hevet/ESP32_radio_evo3/Hardware/Datasheets/3.12 SSD1322 OLED display/312-OLED pure glass dimensions.jpg

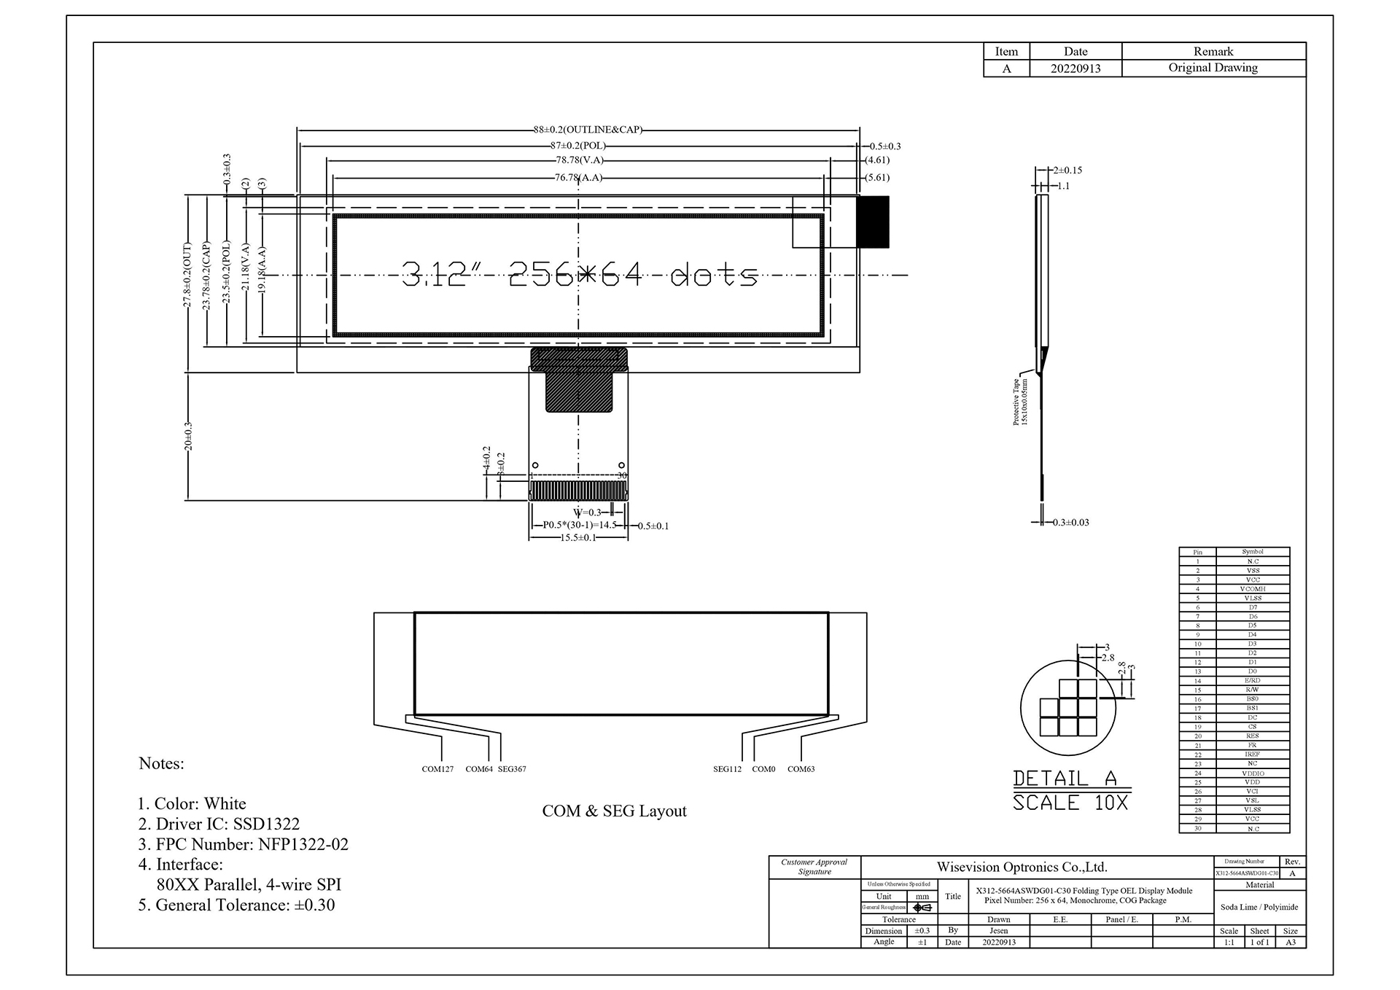
Hardware/Datasheets/3.12 SSD1322 OLED display/312-OLED pure glass dimensions.jpg
