hevet/ESP32_radio_evo3/Hardware/Datasheets/3.12 SSD1322 OLED display/OLED_pinout.png

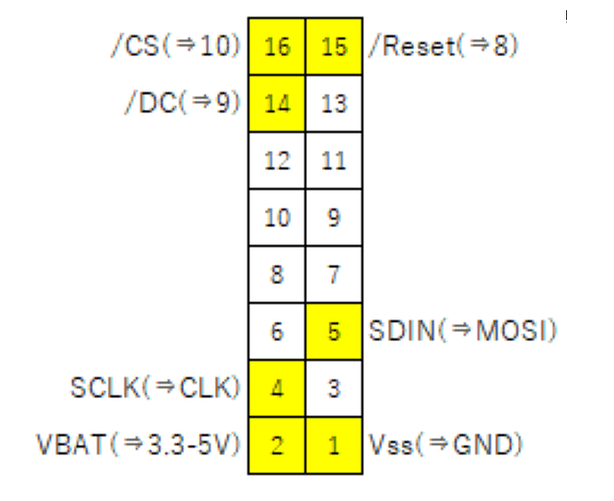
Hardware/Datasheets/3.12 SSD1322 OLED display/OLED_pinout.png
