hevet/ESP32_radio_evo3/Hardware/Datasheets/ESP/esp32 module.webp

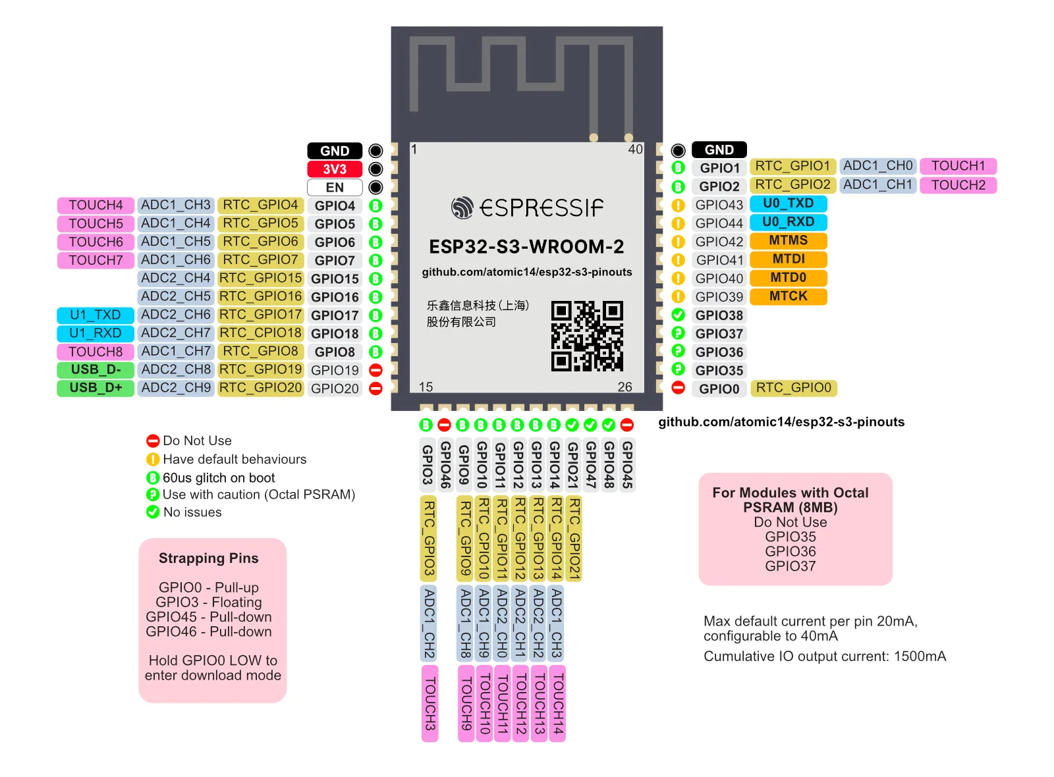
Hardware/Datasheets/ESP/esp32 module.webp
