hevet/ESP32_radio_evo3/Photos/Display1.png

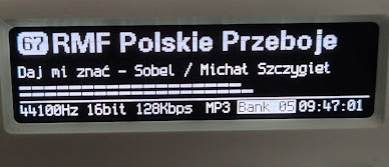
Photos/Display1.png
