hevet/ESP32_radio_evo3/Photos/Display2.png

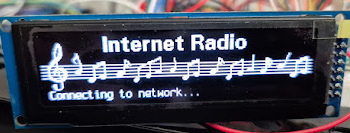
Photos/Display2.png
