hevet/ESP32_radio_evo3/Photos/ESP32_PCB_vis01.png

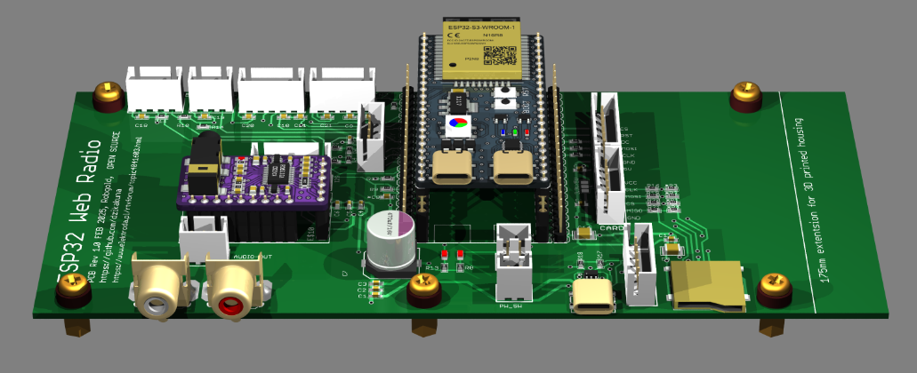
Photos/ESP32_PCB_vis01.png
