hevet/ESP32_radio_evo3/Photos/ESP_radio_rev1.0_PCBvis2.png

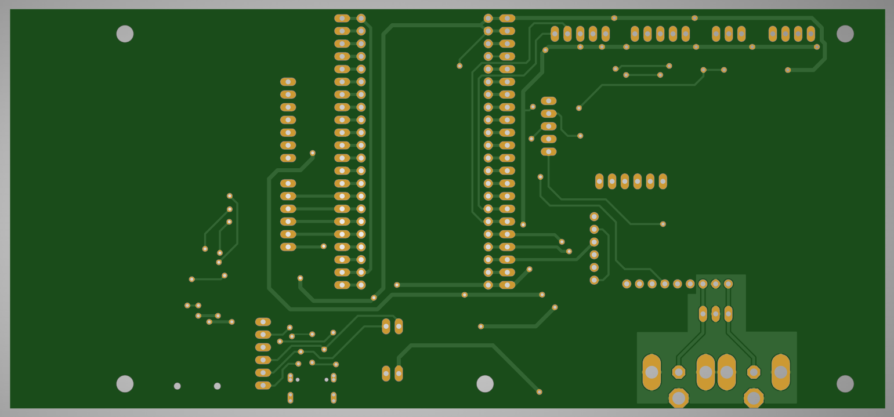
Photos/ESP_radio_rev1.0_PCBvis2.png
