hevet/ESP32_radio_evo3/Photos/Housing1.png

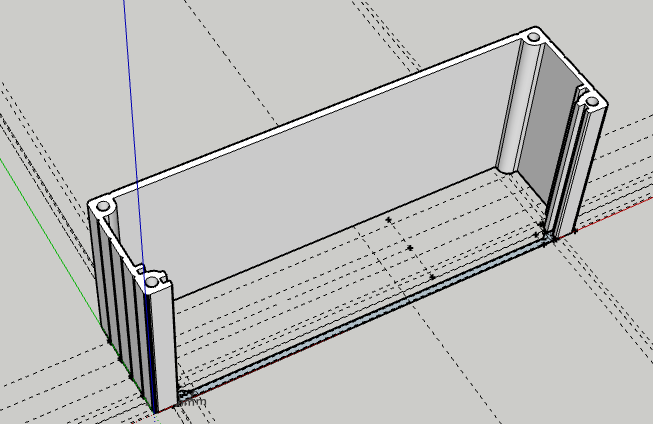
Photos/Housing1.png
