hevet/ESP32_radio_evo3/Photos/Housing3.png

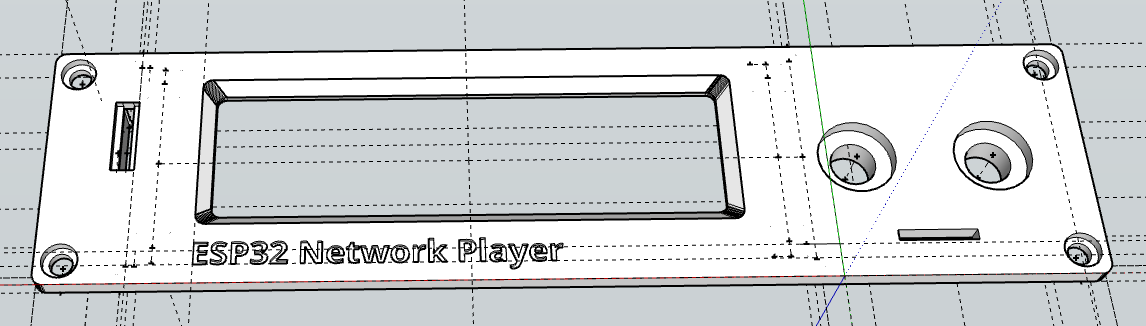
Photos/Housing3.png
