hevet/ESP32_radio_evo3/Photos/Housing4.png

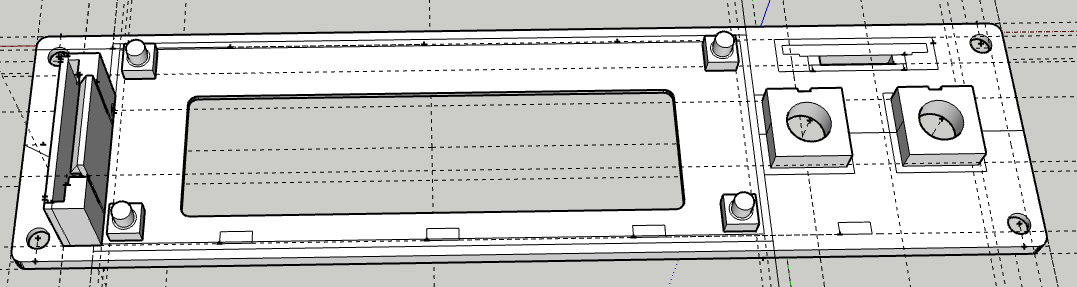
Photos/Housing4.png
