hevet/ESP32_radio_evo3/Photos/RC-406.png

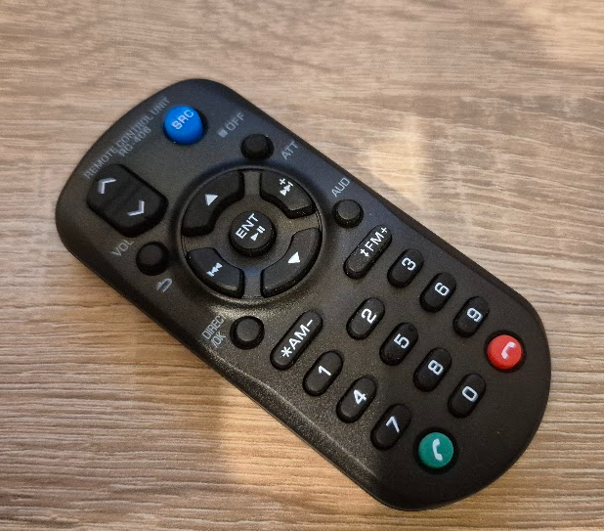
Photos/RC-406.png
