hevet/ESP32_radio_evo3/src/ESP32_radio_evo3.19/Arduino_configuration_from3.17.png

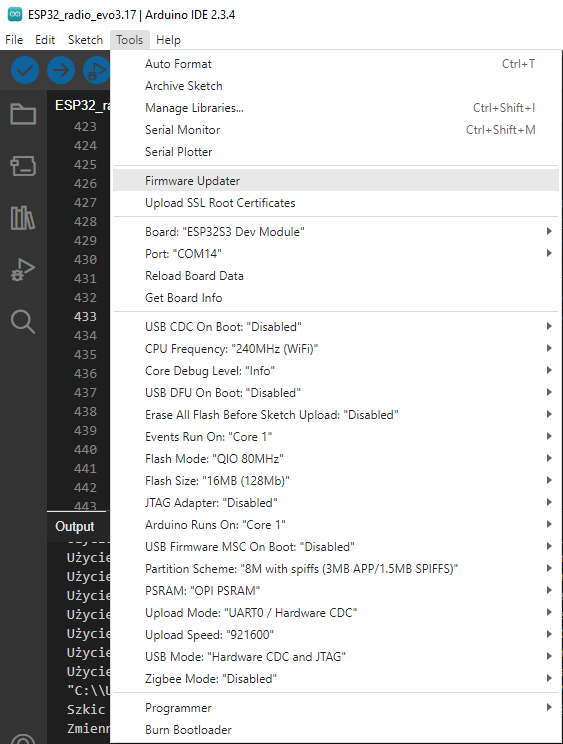
src/ESP32_radio_evo3.19/Arduino_configuration_from3.17.png
