hevet/ESP32_radio_evo3/src/ESP32_radio_evo3.19/Platformio/libdeps/ESP32-audioI2S/additional_info/Breadboard.jpg

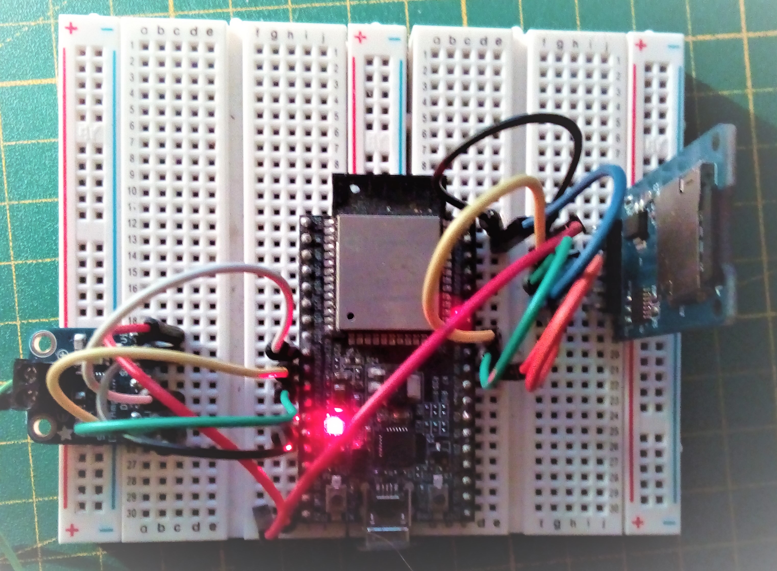
src/ESP32_radio_evo3.19/Platformio/libdeps/ESP32-audioI2S/additional_info/Breadboard.jpg
