hevet/ESP32_radio_evo3/src/ESP32_radio_evo3.19/Platformio/libdeps/ESP32-audioI2S/additional_info/ESP32_I2S_UDA1334A.JPG

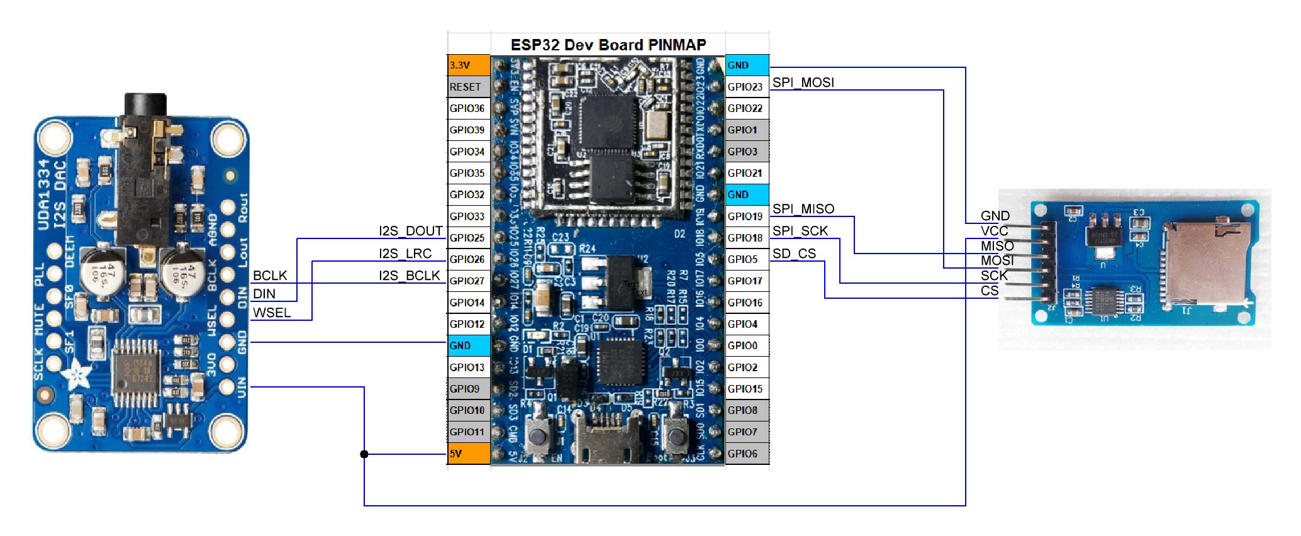
src/ESP32_radio_evo3.19/Platformio/libdeps/ESP32-audioI2S/additional_info/ESP32_I2S_UDA1334A.JPG
