hevet/ESP32_radio_evo3/src/ESP32_radio_evo3.19/Platformio/libdeps/ESP32-audioI2S/additional_info/FLAC Metadata Picture Block.jpg

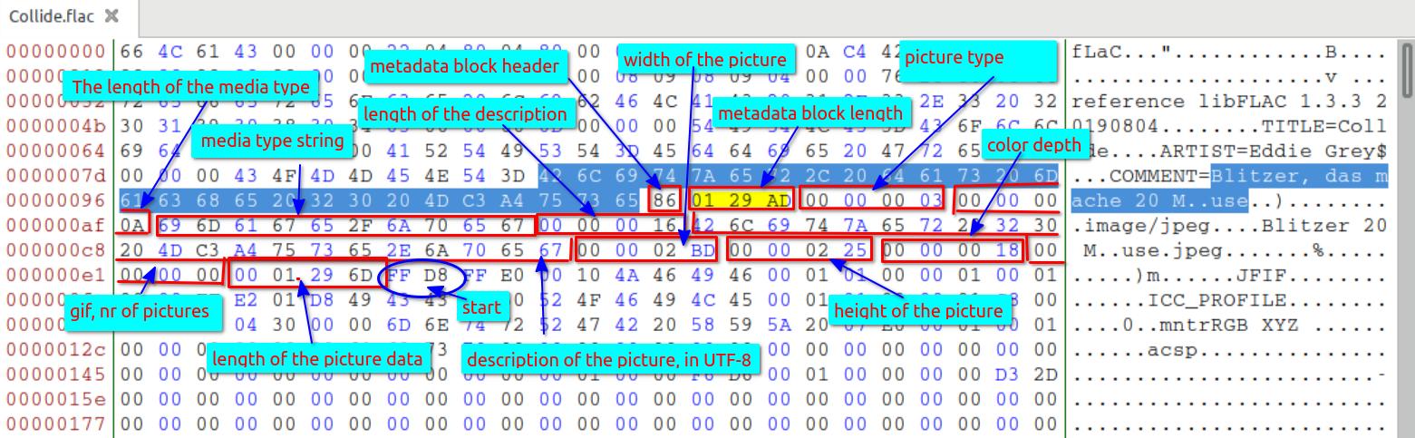
src/ESP32_radio_evo3.19/Platformio/libdeps/ESP32-audioI2S/additional_info/FLAC Metadata Picture Block.jpg
