hevet/ESP32_radio_evo3/src/ESP32_radio_evo3.19/Platformio/libdeps/ESP32-audioI2S/additional_info/Ogg_Metadatapicture.png

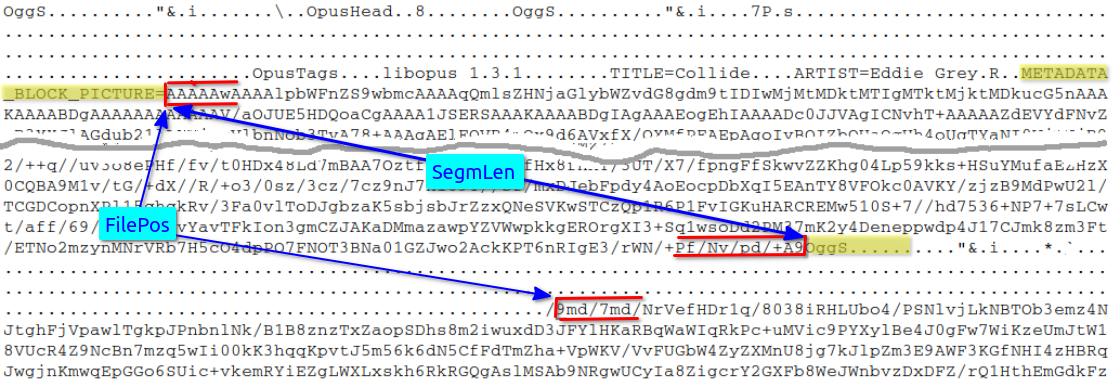
src/ESP32_radio_evo3.19/Platformio/libdeps/ESP32-audioI2S/additional_info/Ogg_Metadatapicture.png
