hevet/ESP32_radio_evo3/src/ESP32_radio_evo3.19/Platformio/libdeps/ESP32-audioI2S/examples/ESP32_A1S/AI-Thinker ESP32-Audio-Kit.jpg

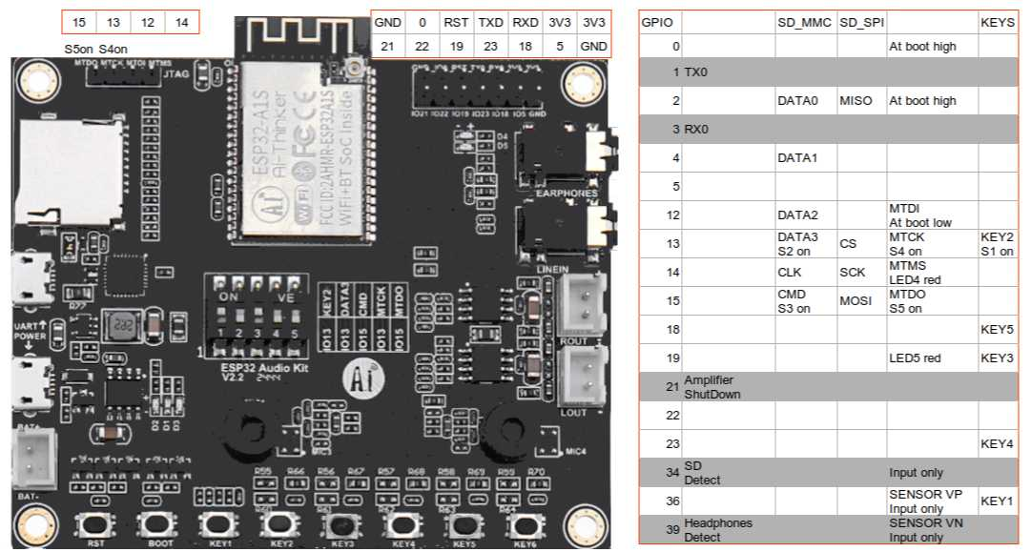
src/ESP32_radio_evo3.19/Platformio/libdeps/ESP32-audioI2S/examples/ESP32_A1S/AI-Thinker ESP32-Audio-Kit.jpg
