hevet/ESP32_radio_evo3/src/ESP32_radio_evo3.19/Platformio/libdeps/ESP32-audioI2S/examples/ESP32_TTGO-TAudio/T9V1.5.jpg

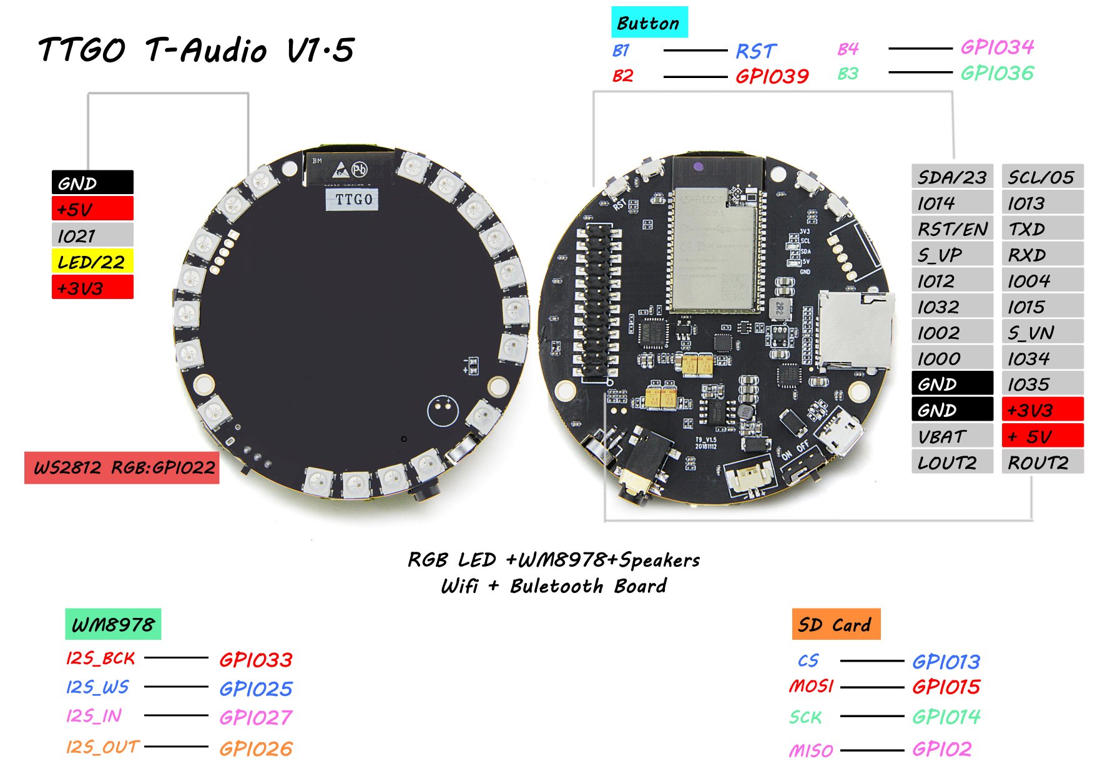
src/ESP32_radio_evo3.19/Platformio/libdeps/ESP32-audioI2S/examples/ESP32_TTGO-TAudio/T9V1.5.jpg
