hevet/ESP32_radio_evo3/src/ESP32_radio_evo3.20/Arduino/ESP32_radio_evo3.20.14.ino

// ################################################################################################################### //
// Evo Internet Radio                                                                                                  //
// ################################################################################################################### //
// Author:   Robgold 2026, Made in Poland                                                                              //
// Source -> https://github.com/dzikakuna/ESP32_radio_evo3/tree/main/src/ESP32_radio_evo3.20                           //
// ################################################################################################################### //
// Platform:                                                                                                           //
// ESP32-S3 DevModule with PSRAM -> best choice ESP32S3-16N8                                                           //
// DAC: PCM5102                                                                                                        //
// OLED Display: 2.08in, 3.12in, 5.5in 256x64px SSD1322, SH1122                                                        //
// 1x or 2x Rotary Encoder                                                                                             //
//                                                                                                                     //
//                                                                                                                     //
// Compilator: Arduino, Platformio                                                                                     //
// ESP32 by Espressif for Arduino:              3.3.8                                                                  //
// ESP32 by Espressif (for lwip recompilation): 5.5.4 - used for FLAC file station TCP/IP lwip recompilation           //
// ESP32-audioI2S-master by schreibfaul1:       3.4.5q with commits 07.05.2026                                         //
// ESP Async WebServer:                         3.10.0                                                                 //
// Async TCP:                                   3.4.10                                                                 // 
// ezButton:                                    1.0.6                                                                  //
// U8g2 by Oliver Olikraus:                     2.35.30                                                                //
// WiFiManager by tzapu                         2.0.17                                                                 //
// ################################################################################################################### //

#include "Arduino.h"           // Standardowy nagłówek Arduino, który dostarcza podstawowe funkcje i definicje
#include <WiFiManager.h>       // Biblioteka do zarządzania konfiguracją sieci WiFi, opis jak ustawić połączenie WiFi przy pierwszym uruchomieniu jest opisany tu: https://github.com/tzapu/WiFiManager
#include <Audio.h>             // Biblioteka do obsługi funkcji związanych z dźwiękiem i audio
#include "SPI.h"               // Biblioteka do obsługi komunikacji SPI
#include "FS.h"                // Biblioteka do obsługi systemu plików
#include <U8g2lib.h>           // Biblioteka do obsługi wyświetlaczy
#include <ezButton.h>          // Biblioteka do obsługi enkodera z przyciskiem
#include <HTTPClient.h>        // Biblioteka do wykonywania żądań HTTP, umożliwia komunikację z serwerami przez protokół HTTP
#include <Ticker.h>            // Mechanizm tickera do odświeżania timera 1s, pomocny do cyklicznych akcji w pętli głównej
#include <EEPROM.h>            // Bilbioteka obsługi emulacji pamięci EEPROM
#include <Time.h>              // Biblioteka do obsługi funkcji związanych z czasem, np. odczytu daty i godziny
#include <ESPAsyncWebServer.h> // Bliblioteka asyncrhionicznego serwera web
#include <AsyncTCP.h>          // Bliblioteka TCP dla serwera web
#include <Update.h>            // Blibioteka dla aktulizacji OTA
#include <ESPmDNS.h>           // Blibioteka mDNS dla ESP

#include "soc/rtc_cntl_reg.h"   // Biblioteki ESP aby móc zrobic pełny reset 
#include "soc/rtc_cntl_struct.h"// Biblioteki ESP aby móc zrobic pełny reset 
#include <esp_sleep.h>
#include "esp_system.h"

#include "esp_heap_caps.h"

#include <freertos/semphr.h>  // Semaphor uzywana w sniferze OLED
#include "esp_sntp.h"         // NTP Sync do sprawdzania stanu

#include "esp_idf_version.h"
//#include "rom/gpio.h"     // Biblioteka do mapowania pinu CS_SD
//#include "esp_wifi.h"     // Biblioteka do ustawienia pasma 20MHz


// --------------- DEFINICJA WERSJI RADIA i NAZWY HOSTA ---------------
#define softwareRev "v3.20.14"  // Wersja oprogramowania radia
#define hostname "evoradio"     // Definicja nazwy hosta widoczna w sieci
// --------------------------------------------------------------------
   
// ################ KONFIGURACJA UZYTKOWNIKA - START ################
//--------------- Typ wysweitlacza OLED ---------------
#define SSD1322     // Wyswietlacz OLED 3.12 cala, SSD1322-256x64px 
//#define SSD1309     // Wyswietlacz OLED 2.42 cala, SSD1309-128x64px TYLKO DisplayMode7 !
//#define SH1122      // Wyswietlacz OLED 2.08 cala, SSD1122-256x64px 
//#define SSD1363     // Wyswietlacz OLED 3.12 cala, SSD1322-256x128px działa ale brak trybu pełnego ekranu
//#define SSD1306     // Wyswietlacz OLED 0.96 cala, SSD1306-128x64px TYLKO DisplayMode7 !

//--------------- SPI wydajnosc pradowa ---------------
//#define LOWNOISESPI   // Ustawia wydajnosc pradowa pinow SPI (0 - najnizsza, niskie szumy; 3-najwyzsza, duze szumy), redukcja EMI

//--------------- OBSLUGA PAMIECI STORAGE ---------------
#define AUTOSTORAGE   // Definicja czy mamy właczony autostorage  (automatyczny wybor karta SD/ pamiec LittleFS lub SPIFFS w zaleznosci od ponizszej delkaracji)
#define USE_SD        // Uzywamy karty SD , zostawiamy w przypadku AUTOSTORAGE lub gdy chcemy tylko uzywać karty SD
//#define USE_SPIFFS  // Definijuemy czy w przypadku uzywania pamieci wewnetrznej bedzie to SPIFFS czy LittleFS. Odkomentowac TYLKO jedno LittleFS lub SPIFFS !
#define USE_LittleFS  // Patrz powyzej

//--------------- DRUGI ENKODER ---------------
//#define twoEncoders // Wlaczamy drugi enkoder

//--------------- DODATKi developerskie - Komunikacja RS232, Wzmacniacz TAS, sniffer OLED itp. ---------------
//#define SERIALCOM   // Komunikacja dwukierunkowa RS232
//#define TAS5805       // Kompilacja dla wersji ze Wzmacniacz TAS5805 z wbudowanym DAC, zakomentowac w przypadku tandardowe PCM5102
//#define OLED_SNIFF

//--------------- PRZYCISKI i LEDy definicja ---------------
//#define SW_POWER 8           // Dedykowany przycisk Power
#define STANDBY_LED 17         // LED do informowania o trybie Standby
#define IR_LED 17              // LED aktywności odbiornika IR
#define ADC_KEYBOARD_PIN 9     // GPIO Klawiatury ADC
//#define SD_LED 17            // LED aktywnosci karty SD, sygnalizacja syngału CS karty, klon pinu uzyteczny w przypadku uzywania czytnika SD
#define IR_LED_ON 0
#define IR_LED_OFF 1
#define STANDBY_LED_ON 0     // Stan GPIO LED STANDBY gdy radio w trybie SLEEP/OFF
#define STANDBY_LED_OFF 1    // Stan GPIO LED gdy radio ON

// --------------- AMP Control ---------------
#define AMP  // Wlaczenie GPIO do obslugi zalaczenia wzmacniacza 
#ifdef AMP
  #define AMP_CTRL 16 // Pin do kontroli wzmacniacza PWR lub Mute
  #define AMP_CTRL_LEVEL 1 // Poziom logiczny jaki mamy na wyjsciu AMP_CTRL przy wlaczonym radiu
#endif


// --------------- INNE ---------------
const bool f_logoSlowBrightness = 1; // Zalaczenie powolnego rozjasniania logo

// ################ KONFIGURACJA UZYTKOWNIKA - KONIEC ################


// --------------- OLED LIVE SNIFFER ---------------
#ifdef OLED_SNIFF
  //#define FB_SIZE (256*64/8)
  #include <freertos/semphr.h>
  #include "oledsniff.h"
  uint8_t snifferBuffer[FB_SIZE];
  uint8_t framebuffer[FB_SIZE];        // bufor
  SemaphoreHandle_t fbMutex;           // mutex do bezpiecznego dostępu
#endif

// --------------- TAS5805 ---------------
#ifdef TAS5805 //PowerAmp with I2S & DSP                 
  #include <Wire.h>           // I2C dla komunikacji z TI TAS5805
  #define I2C_CLK 9           // GPIO CLOCK I2C
  #define I2C_DATA 8          // GPIO DATA I2C
  #define TAS5805_ADDR 0x2D   // Adres I2C TAS5805, pull-up na ADR/#FAULT 10k podbicie adresu o 1
  
  // --------------- TAS5805 - definicja pinow AMPa z przetwornikiem ---------------
  #define I2S_DOUT 16        // Podłączenie do pinu DIN na DAC TAS
  #define I2S_BCLK 14        // Podłączenie po pinu BCK na DAC TAS
  #define I2S_LRC 15         // Podłączenie do pinu LCK na DAC TAS
  // --------------- IR odbiornik podczerwieni --------------- 
  #define recv_pin 7        // Odbiornik IR

#else // --------------- PCM5102A ---------------
  // --------------- PCM5102A - definicja pinow przetwornika ---------------
  #define I2S_DOUT 13             // Podłączenie do pinu DIN na DAC
  #define I2S_BCLK 12             // Podłączenie po pinu BCK na DAC
  #define I2S_LRC 14              // Podłączenie do pinu LCK na DAC 
  //#define I2S_MCLK 18           // Pełny I2S z MCLK dla SPDIF/TOSLINK
  
  // --------------- IR odbiornik podczerwieni ---------------
  #define recv_pin 15 // Odbiornik IR
#endif


// --------------- CZYTNIK KART SD (Opcjonalny) ---------------
#define SD_CS 47    // Pin CS (Chip Select) dla karty SD wybierany jako interfejs SPI
#define SD_SCLK 45  // Pin SCK (Serial Clock) dla karty SD
#define SD_MISO 21  // Pin MISO (Master In Slave Out) dla karty SD
#define SD_MOSI 48  // pin MOSI (Master Out Slave In) dla karty SD

// ------ AUTO WYKRYWANIE STORAGE - Karta SD / LittleFS -----
#ifdef AUTOSTORAGE
  
  #ifdef USE_SPIFFS 
    #include "SPIFFS.h"
  #endif

  #ifdef USE_LittleFS
    #include "LittleFS.h"
  #endif
  
  #include "SD.h"
  #define STORAGE (*_storage)
  bool initStorage();
  bool useSD = false;
  const char* storageTextName = nullptr;
  fs::FS* _storage = nullptr;
#else
  #ifdef USE_SD
    #include "SD.h"
    #define STORAGE SD
    #define STORAGE_BEGIN() SD.begin(SD_CS, customSPI)
    const bool useSD = true;
    #define storageTextName "SD      "

  #elif defined(USE_LittleFS) 
    #include "LittleFS.h"
    #define STORAGE LittleFS
    #define STORAGE_BEGIN() LittleFS.begin(true)  // Dla LittleFS, stabilniej działa i nie przerywa audio
    const bool useSD = false;
    #define storageTextName "LittleFS"
  
  #elif defined(USE_SPIFFS)
    #include "SPIFFS.h" 
    #define STORAGE LittleFS
    #define STORAGE_BEGIN() SPIFFS.begin(true)  // Stary system plikow dla kompatybilnosci
    const bool useSD = false;
    #define storageTextName "SPIFFS  "
  #endif 
#endif
 
// --------------- OLED Wyswietlacz - definicja pinow ---------------
#define SPI_MOSI_OLED 39  // Pin MOSI (Master Out Slave In) dla interfejsu SPI OLED
#define SPI_MISO_OLED 0   // Pin MISO (Master In Slave Out) brak dla wyswietlacza OLED
#define SPI_SCK_OLED 38   // Pin SCK (Serial Clock) dla interfejsu SPI OLED
#define CS_OLED 42        // Pin CS (Chip Select) dla interfejsu OLED
#define DC_OLED 40        // Pin DC (Data/Command) dla interfejsu OLED
#define RESET_OLED 41//-1 //41     // Pin Reset dla interfejsu OLED


// Rozmiar wysweitlacz OLED (potrzebny do wyświetlania grafiki)
#define SCREEN_WIDTH 256        // Szerokość ekranu w pikselach
#define SCREEN_HEIGHT 64        // Wysokość ekranu w pikselach

 

// --------------- ENCODER 2 (MAIN) ---------------
// Jesli jedyny to Volume/Stacje/Banki/PowerOff/PowerOn jesli z Enkoderem1 to Stacje/Banki
#define CLK_PIN2 10             // Podłączenie z pinu 10 do CLK na enkoderze
#define DT_PIN2 11              // Podłączenie z pinu 11 do DT na enkoderze lewym
#define SW_PIN2 1               // Podłączenie z pinu 1 do SW na enkoderze lewym (przycisk)

// --------------- ENCODER 1 (dodatkowy) ---------------
// Jesli zdefinionway to Volume/Mute/PowerOff/PowerOn
#ifdef twoEncoders
  #define CLK_PIN1 6              // Podłączenie z pinu 6 do CLK na enkoderze prawym
  #define DT_PIN1 5               // Podłączenie z pinu 5 do DT na enkoderze prawym
  #define SW_PIN1 4               // Podłączenie z pinu 4 do SW na enkoderze prawym (przycisk)
  const bool use2encoders = true;
  // Zmienne enkodera 1
  int CLK_state1 = 0;
  int prev_CLK_state1 = 0;
  int buttonLongPressTime1 = 150;
  int buttonSuperLongPressTime1 = 2000;
  bool action4Taken = false;        // Flaga Akcji 4 - enkoder 1, powerOFF
  bool action5Taken = false;        // Flaga Akcji 5 - enkoder 1, Menu Bank
#else
  const bool use2encoders = false;
#endif


// --------------- USTAWIENIE TIMERa dla trybu POWEROFF --------------- 
#define WAKEUP_INTERVAL_US (60ULL * 1000000ULL) // 1 minuta

// definicja dlugosci ilosci stacji w banku, dlugosci nazwy stacji w PSRAM/EEPROM, maksymalnej ilosci plikow audio (odtwarzacz)
#define MAX_STATIONS 99          // Maksymalna liczba stacji radiowych, które mogą być przechowywane w jednym banku
#define STATION_NAME_LENGTH 220  // Nazwa stacji wraz z bankiem i numerem stacji do wyświetlenia w pierwszej linii na ekranie
#define MAX_FILES 100            // Maksymalna liczba plików lub katalogów w tablicy directoriesz
#define bank_nr_max 16           // Numer jaki może osiągnac maksymalnie zmienna bank_nr czyli ilość banków
#define displayModeMax 6         // Ogrniczenie maksymalnej ilosci trybów wyswietlacza OLED

// DEBUG PRINTS - ON/OFF
#define f_debug_web_on 0         // Flaga właczenia wydruku debug_web
#define f_debug_on 0             // Flaga właczenia wydruku debug

//String STATIONS_URL1 = "https://raw.githubusercontent.com/dzikakuna/ESP32_radio_streams/main/bank01.txt";   // Adres URL do pliku z listą stacji radiowych
#define STATIONS_URL1  "https://raw.githubusercontent.com/dzikakuna/ESP32_radio_streams/main/bank01.txt"  // Adres URL do pliku z listą stacji radiowych
#define STATIONS_URL2  "https://raw.githubusercontent.com/dzikakuna/ESP32_radio_streams/main/bank02.txt"  // Adres URL do pliku z listą stacji radiowych
#define STATIONS_URL3  "https://raw.githubusercontent.com/dzikakuna/ESP32_radio_streams/main/bank03.txt"  // Adres URL do pliku z listą stacji radiowych
#define STATIONS_URL4  "https://raw.githubusercontent.com/dzikakuna/ESP32_radio_streams/main/bank04.txt"  // Adres URL do pliku z listą stacji radiowych
#define STATIONS_URL5  "https://raw.githubusercontent.com/dzikakuna/ESP32_radio_streams/main/bank05.txt"  // Adres URL do pliku z listą stacji radiowych
#define STATIONS_URL6  "https://raw.githubusercontent.com/dzikakuna/ESP32_radio_streams/main/bank06.txt"  // Adres URL do pliku z listą stacji radiowych
#define STATIONS_URL7  "https://raw.githubusercontent.com/dzikakuna/ESP32_radio_streams/main/bank07.txt"  // Adres URL do pliku z listą stacji radiowych
#define STATIONS_URL8  "https://raw.githubusercontent.com/dzikakuna/ESP32_radio_streams/main/bank08.txt"  // Adres URL do pliku z listą stacji radiowych
#define STATIONS_URL9  "https://raw.githubusercontent.com/dzikakuna/ESP32_radio_streams/main/bank09.txt"  // Adres URL do pliku z listą stacji radiowych
#define STATIONS_URL10 "https://raw.githubusercontent.com/dzikakuna/ESP32_radio_streams/main/bank10.txt"  // Adres URL do pliku z listą stacji radiowych
#define STATIONS_URL11 "https://raw.githubusercontent.com/dzikakuna/ESP32_radio_streams/main/bank11.txt"  // Adres URL do pliku z listą stacji radiowych
#define STATIONS_URL12 "https://raw.githubusercontent.com/dzikakuna/ESP32_radio_streams/main/bank12.txt"  // Adres URL do pliku z listą stacji radiowych
#define STATIONS_URL13 "https://raw.githubusercontent.com/dzikakuna/ESP32_radio_streams/main/bank13.txt"  // Adres URL do pliku z listą stacji radiowych
#define STATIONS_URL14 "https://raw.githubusercontent.com/dzikakuna/ESP32_radio_streams/main/bank14.txt"  // Adres URL do pliku z listą stacji radiowych
#define STATIONS_URL15 "https://raw.githubusercontent.com/dzikakuna/ESP32_radio_streams/main/bank15.txt"  // Adres URL do pliku z listą stacji radiowych
#define STATIONS_URL16 "https://raw.githubusercontent.com/dzikakuna/ESP32_radio_streams/main/bank16.txt"  // Adres URL do pliku z listą stacji radiowych
#define STATIONS_URL17 "https://raw.githubusercontent.com/dzikakuna/ESP32_radio_streams/main/bank17.txt"  // Adres URL do pliku z listą stacji radiowych
#define STATIONS_URL18 "https://raw.githubusercontent.com/dzikakuna/ESP32_radio_streams/main/bank18.txt"  // Adres URL do pliku z listą stacji radiowych


// --------------- DEFINICJA TEKSTOW ---------------
#define SLEEP_STRING "SLEEP "
#define SLEEP_STRING_VAL " MINUTES"
#define SLEEP_STRING_OFF "OFF"

#ifdef LANG_EN
static const char* months[] = {
    "JANUARY",
    "FEBRUARY",
    "MARCH",
    "APRIL",
    "MAY",
    "JUNE",
    "JULY",
    "AUGUST",
    "SEPTEMBER",
    "OCTOBER",
    "NOVEMBER",
    "DECEMBER"
};
#endif

// --------------- KOMUNIKACJA MODUŁU RADIA PO RS232 ---------------
#ifdef SERIALCOM
  #include "serialcom.h"   // Integracja jako moduł z komunikacja po RS232
#endif


// --------------- Zmienne  DLA PILOTa IR w standardzie NEC - przeniesiona do pliku txt ---------------
uint16_t rcCmdVolumeUp = 0;   // Głosnosc +
uint16_t rcCmdVolumeDown = 0; // Głośnosc -
uint16_t rcCmdArrowRight = 0; // strzałka w prawo - nastepna stacja
uint16_t rcCmdArrowLeft = 0;  // strzałka w lewo - poprzednia stacja  
uint16_t rcCmdArrowUp = 0;    // strzałka w góre - lista stacji krok do gory
uint16_t rcCmdArrowDown = 0;  // strzałka w dół - lista stacj krok na dół
uint16_t rcCmdBack = 0;	      // Przycisk powrotu
uint16_t rcCmdOk = 0;         // Przycisk Ent - zatwierdzenie stacji
uint16_t rcCmdSrc = 0;        // Przełączanie źródła radio, odtwarzacz
uint16_t rcCmdMute = 0;       // Wyciszenie dzwieku
uint16_t rcCmdAud = 0;        // Equalizer dzwieku
uint16_t rcCmdDirect = 0;     // Janość ekranu, dwa tryby 1/16 lub pełna janość     
uint16_t rcCmdBankMinus = 0;  // Wysweitla wybór banku
uint16_t rcCmdBankPlus = 0;   // Wysweitla wybór banku
uint16_t rcCmdRed = 0;        // Przełacza ładowanie banku kartaSD - serwer GitHub w menu bank
uint16_t rcCmdGreen = 0;      // VU wyłaczony, VU tryb 1, VU tryb 2, zegar
uint16_t rcCmdKey0 = 0;       // Przycisk "0"
uint16_t rcCmdKey1 = 0;       // Przycisk "1"
uint16_t rcCmdKey2 = 0;       // Przycisk "2"
uint16_t rcCmdKey3 = 0;       // Przycisk "3"
uint16_t rcCmdKey4 = 0;       // Przycisk "4"
uint16_t rcCmdKey5 = 0;       // Przycisk "5"
uint16_t rcCmdKey6 = 0;       // Przycisk "6"
uint16_t rcCmdKey7 = 0;       // Przycisk "7"
uint16_t rcCmdKey8 = 0;       // Przycisk "8"
uint16_t rcCmdKey9 = 0;       // Przycisk "9"
uint16_t rcCmdPower = 0;       // Przycisk Power
// Koniec definicji pilota IR

bool  f_callInfo = 0;       // Flaga czy wsiwetlamy "INFO" również na OLED
bool  f_logo = 0;           // Flaga czy wyswietlamy logo
bool  f_simpleMode3 =0;

int currentSelection = 0;                     // Numer aktualnego wyboru na ekranie OLED
int firstVisibleLine = 0;                     // Numer pierwszej widocznej linii na ekranie OLED
uint8_t station_nr = 0;                       // Numer aktualnie wybranej stacji radiowej z listy
int stationFromBuffer = 0;                    // Numer stacji radiowej przechowywanej w buforze do przywrocenia na ekran po bezczynności
uint8_t bank_nr;                              // Numer aktualnie wybranego banku stacji z listy
uint8_t previous_bank_nr = 0;                 // Numer banku przed wejsciem do menu zmiany banku
//int bankFromBuffer = 0;                       // Numer aktualnie wybranego banku stacji z listy do przywrócenia na ekran po bezczynności

//Enkoder 2 (podstawowy)
int CLK_state2;                               // Aktualny stan CLK enkodera lewego
int prev_CLK_state2;                          // Poprzedni stan CLK enkodera lewego
int stationsCount = 0;                        // Aktualna liczba przechowywanych stacji w tablicy
int buttonLongPressTime2 = 2000;              // Czas reakcji na długie nacisniecie enkoder 2
int buttonShortPressTime2 = 500;              // Czas rekacjinna krótkie nacisniecie enkodera 2
int buttonSuperLongPressTime2 = 3000;         // Czas reakcji na super długie nacisniecie enkoder 2

uint8_t volumeValue = 10;                     // Wartość głośności, domyślnie ustawiona na 10
uint8_t maxVolume = 21;
bool maxVolumeExt =  false;                   // 0(false) -  zakres standardowy Volume 1-21 , 1 (true) - zakres rozszerzony 0-42
uint8_t volumeBufferValue = 0;                // Wartość głośności, jako bufor w przypadku gdy nie zapisujemy za kazdym razem przy zmianie volumeValue, słuzy do porownania w momencie zapisu czy nastapila zmiana
int maxVisibleLines = 4;                      // Maksymalna liczba widocznych linii na ekranie OLED
int bitrateStringInt = 0;                     // Deklaracja zmiennej do konwersji Bitrate string na wartosc Int aby podzelic bitrate przez 1000
int SampleRate = 0;
int SampleRateRest = 0;
int audioBufferTime = 0;                      // Zienna trzymajca informacje o ilosci sekund muzyki w buforze audio

uint8_t stationNameLenghtCut = 24;            // 24-> 25 znakow, 25-> 26 znaków, zmienna określająca jak długa nazwę ma nazwa stacji w plikach Bankow liczone od 0- wartosci ustalonej
const uint8_t yPositionDisplayScrollerMode0 = 33;   // Wysokosc (y) wyswietlania przewijanego/stalego tekstu stacji w danym trybie
const uint8_t yPositionDisplayScrollerMode1 = 61;   // Wysokosc (y) wyswietlania przewijanego/stalego tekstu stacji w danym trybie
const uint8_t yPositionDisplayScrollerMode2 = 25;   // Wysokosc (y) wyswietlania przewijanego/stalego tekstu stacji w danym trybie
const uint8_t yPositionDisplayScrollerMode3 = 49;   // Wysokosc (y) wyswietlania przewijanego/stalego tekstu stacji w danym trybie
const uint8_t yPositionDisplayScrollerMode5 = 35;   // Wysokosc (y) wyswietlania przewijanego/stalego tekstu stacji w danym trybie
const uint8_t stationNamePositionYmode3 = 31;
const uint8_t stationNamePositionYmode5 = 26;
uint16_t stationStringScrollLength = 0;
uint8_t maxStationVisibleStringScrollLength = 46;
bool stationNameFromStream = 0;               // Flaga definiujaca czy wyswietlamy nazwe stacji z plikow Banku pamieci czy z informacji nadawanych w streamie
bool f_powerOff = 0;                          // Flaga aktywnego trybu power off (ESP light sleep)
bool f_sleepTimerOn = false;
uint8_t sleepTimerValueSet = 0;           // Zmiena przechowujaca ustawiony czas - nie uzywana obecnie
uint8_t sleepTimerValueCounter = 0;         // Licznik funkcji sleep timer dekrementowany przez Timer3 co 1 minute
uint8_t sleepTimerValueStep = 15;           // Krok funkcji sleep timer o ile zwieksza się timer
uint8_t sleepTimerValueMax = 90;            // Maksymalna wartosc sleep timera jaka da się ustawić
//uint8_t bank_nr_max = 16;


// ---- Głosowe odtwarzanie czasu co godzinę ---- //
bool f_requestVoiceTimePlay = false; 
bool timeVoiceInfoEveryHour = true;
unsigned long voiceTimeMillis = 0;
uint16_t voiceTimeReturnTime = 4000;


// ---- Auto dimmer / auto przyciemnianie wyswietlacza ---- //
uint8_t displayDimmerTimeCounter = 0;  // Zmienna inkrementowana w przerwaniu timera2 do przycimniania wyswietlacz
uint8_t dimmerDisplayBrightness = 10;   // Wartość przyciemnienia wyswietlacza po czasie niekatywnosci
uint8_t dimmerSleepDisplayBrightness = 1; // Wartość przyciemnienia wyswietlacza po czasie niekatywnosci
uint8_t displayBrightness = 180;        // Domyślna maksymalna janość wyswietlacza
uint16_t displayAutoDimmerTime = 5;   // Czas po jakim nastąpi przyciemninie wyswietlacza, liczony w sekundach
bool displayAutoDimmerOn = false;       // Automatyczne przyciemnianie wyswietlacza, domyślnie włączone
bool displayDimmerActive = false;       // Aktywny tryb przyciemnienia
uint16_t displayPowerSaveTime = 30;    // Czas po jakim zostanie wyłączony wyswietlacz OLED (tryb power save)
uint16_t displayPowerSaveTimeCounter = 0;    // Timer trybu Power Save wyswietlacza OLED
bool displayPowerSaveEnabled = false;   // Flaga okreslajaca czy tryb wyłączania wyswietlacza OLED jest właczony
uint8_t displayMode = 0;               // Tryb wyswietlacza 0-displayRadio z przewijaniem "scroller" / 1-Zegar / 2- tryb 3 stałych linijek tekstu stacji

// ---- Equalzier ---- //
int8_t toneLowValue = 0;               // Wartosc filtra dla tonow niskich
int8_t toneMidValue = 0;               // Wartosc flitra dla tonow srednich
int8_t toneHiValue = 0;                // Wartość filtra dla tonow wysokich
int8_t balanceValue = 0;                // Wartość balansu
uint8_t toneSelect = 1;                // Zmienna okreslająca, który filtr equalizera regulujemy, startujemy od pierwszego

bool equalizerMenuEnable = false;      // Flaga wyswietlania menu Equalizera

// ------ Wprowadzaeni cyfr z pilota / klawiatury ------ //
uint8_t rcInputDigit1 = 0xFF;      // Pierwsza cyfra w przy wprowadzaniu numeru stacji z pilota
uint8_t rcInputDigit2 = 0xFF;      // Druga cyfra w przy wprowadzaniu numeru stacji z pilota
bool f_Presets = false;            // Flaga Preset okreslajaca czy przelaczamy stacje czy wprowadzamy numer stacji jako cyfry


// ---- Zmienne konfiguracji ---- //
#define CONFIG_COUNT 27                                  // Dlugosc konfiguracji radia
uint16_t configArray[CONFIG_COUNT] = {0};
uint8_t rcPage = 0;
#define CONFIGREMOTE_COUNT 26                           // Dlugosc konfiguracji pilota IR
uint16_t configRemoteArray[CONFIGREMOTE_COUNT] = {0};   // Tablica przechowująca kody pilota podczas odczytu z pliku


uint16_t configAdcArray[24] = {0};        // Tablica przechowująca wartosci ADC dla przyciskow klawiatury
bool configExist = true;                  // Flaga okreslajaca czy istnieje plik konfiguracji
bool f_displayPowerOffClock = false;      // Flaga okreslajaca czy w trybie sleep ma się wyswietlac zegar
bool f_sleepAfterPowerFail = false;       // Flaga czy idziemy do powerOFF po powrocie zasilania
bool f_saveVolumeStationAlways = true;    // Flaga określająca czy zapisujemy stacje, bank i poziom volume zawsze czy tylko przy power OFF
bool f_powerOffAnimation = false;         // Animacja przy power OFF
bool remoteConfig = false;

bool encoderButton2 = false;      // Flaga określająca, czy przycisk enkodera 2 został wciśnięty
bool encoderFunctionOrder = false; // Flaga okreslająca kolejność funkcji enkodera 2
bool displayActive = false;       // Flaga określająca, czy wyświetlacz jest aktywny

bool mp3 = false;                 // Flaga określająca, czy aktualny plik audio jest w formacie MP3
bool flac = false;                // Flaga określająca, czy aktualny plik audio jest w formacie FLAC
bool aac = false;                 // Flaga określająca, czy aktualny plik audio jest w formacie AAC
bool vorbis = false;              // Flaga określająca, czy aktualny plik audio jest w formacie VORBIS
bool opus = false;
bool timeDisplay = true;          // Flaga określająca kiedy pokazać czas na wyświetlaczu, domyślnie od razu po starcie
bool listedStations = false;      // Flaga określająca czy na ekranie jest pokazana lista stacji do wyboru
bool bankMenuEnable = false;      // Flaga określająca czy na ekranie jest wyświetlone menu wyboru banku
bool bitratePresent = false;      // Flaga określająca, czy na serial terminalu pojawiła się informacja o bitrate - jako ostatnia dana spływajaca z info
bool bankNetworkUpdate = false;   // Flaga wyboru aktualizacji banku z sieci lub karty SD - True aktulizacja z interNETu
bool volumeMute = false;          // Flaga okreslająca stan funkcji wyciszczenia - Mute
bool volumeSet = false;           // Flaga wejscia menu regulacji głosnosci na enkoderze 2

bool action3Taken = false;        // Flaga Akcji 3

bool ActionNeedUpdateTime = false;// Zmiena okresaljaca dla displayRadio potrzebe odczytu aktulizacji czasu
bool debugAudioBuffor = false;    // Wyswietlanie bufora Audio
bool f_audioInfoRefreshStationString = false;    // Flaga wymuszjąca wymagane odsiwezenie ze względu na zmianę info stream - stationstring, title, 
bool f_audioInfoRefreshDisplayRadio = false;    // Flaga wymuszjąca wymagane odsiwezenie ze względu na zmianę info stream - linia kbps, khz, format streamu
bool resumePlay = false;            // Flaga wymaganego uruchomienia odtwarzania po zakonczeniu komunikatu głosowego
bool fwupd = false;               // Flaga blokujaca main loop podczas aktualizacji oprogramowania
bool configIrExist = false;       // Flaga informująca o istnieniu poprawnej konfiguracji pilota IR
bool wsAudioRefresh = false;      // Flaga informujaca o potrzebe odswiezeninia Station Text za pomoca Web Sokcet
bool f_voiceTimeBlocked = false;
bool f_displaySleepTime = false;    // Flaga wysiwetlania menu timera
bool f_displaySleepTimeSet = false;    // Flaga ustawienia sleep timera

bool noSDcard = false;              // flaga ustawiana przy braku wykrycia karty SD
bool noStorage = false;             // flaga ustawiana przy problemie z pamiecia SPIFFS/LittleFS

bool f_changeStationWithoutEncoderClick = false; // faga ustalajca reakcje czy automatycznie zmieniamy stacje po wybraniu na liscie stacji

unsigned long debounceDelay = 300;    // Czas trwania debouncingu w milisekundach
unsigned long displayTimeout = 3000;  // Czas wyświetlania komunikatu na ekranie w milisekundach
unsigned long displayStartTime = 0;   // Czas rozpoczęcia wyświetlania komunikatu
unsigned long seconds = 0;            // Licznik sekund timera
unsigned int PSRAM_lenght = MAX_STATIONS * (STATION_NAME_LENGTH) + MAX_STATIONS; // deklaracjia długości pamięci PSRAM
unsigned long lastCheckTime = 0;      // No stream audio blink
//uint8_t stationNameStreamWidth = 0;   // Test pełnej nazwy stacji
uint64_t seconds2nextMinute;
uint64_t micros2nextMinute;

// ---- VU Meter ---- //
unsigned long vuMeterTime;                 // Czas opznienia odswiezania wskaznikow VU w milisekundach
uint8_t vuMeterL;                          // Wartosc VU dla L kanału zakres 0-255
uint8_t vuMeterR;                          // Wartosc VU dla R kanału zakres 0-255
uint8_t peakL = 0;                         // Wartosc peakHold dla kanalu lewego
uint8_t peakR = 0;                         // Wartosc peakHold dla kanalu prawego
uint8_t peakHoldTimeL = 0;                 // Licznik peakHold dla kanalu lewego
uint8_t peakHoldTimeR = 0;                 // Licznik peakHold dla kanalu prawego
const uint8_t peakHoldThreshold = 5;       // Liczba cykli zanim peak opadnie
const uint8_t vuLy = 41;                   // Koordynata Y wskaznika VU L-lewego (wyzej)
const uint8_t vuRy = 47;                   // Koordynata Y wskaznika VU R-prawego (nizej)
const uint8_t vuLyMode3 = 54;              // Koordynata Y wskaznika VU L-lewego (wyzej)
const uint8_t vuRyMode3 = 60;              // Koordynata Y wskaznika VU R-prawego (nizej
const uint8_t vuLyMode5 = 43;                   // Koordynata Y wskaznika VU L-lewego (wyzej)
const uint8_t vuRyMode5 = 49;                   // Koordynata Y wskaznika VU R-prawego (nizej)
const uint8_t vuThicknessMode3 = 1;        // Grubosc kreseczki wskaznika VU w trybie Mode3
const int vuCenterXmode3 = 128;            // Pozycja centralna startu VU w trybie Mode 3
const int vuYmode3 = 62;                   // Polozenie wyokosci (Y) VU w trybie Mode 3
bool vuPeakHoldOn = 1;                     // Flaga okreslajaca czy funkcja Peak & Hold na wskazniku VUmeter jest wlaczona
bool vuMeterOn = true;                     // Flaga właczajaca wskazniki VU
bool vuMeterMode = false;                  // tryb rysowania vuMeter
uint8_t displayVuL = 0;                    // wartosc VU do wyswietlenia po procesie smooth
uint8_t displayVuR = 0;                    // wartosc VU do wyswietlenia po procesie smooth
uint8_t vuRiseSpeed = 24;                  // szybkość narastania VU
uint8_t vuFallSpeed = 6;                   // szybkość opadania VU
bool vuSmooth = 1;                         // Flaga zalaczenia funkcji smootht (domyslnie wlaczona=1)
uint8_t vuRiseNeedleSpeed = 2;                  // szybkość narastania VU
uint8_t vuFallNeedleSpeed = 6;                   // szybkość opadania VU
bool reversColorMode4 = true;

// Volume Fade
unsigned long lastFadeTime = 0;
const unsigned long fadeStepDelay = 20; // ms
bool fadingIn = false;
uint8_t targetVolume = 0;
uint8_t currentVolume = 0;
bool f_volumeFadeOn = 0;
uint8_t volumeFadeOutTime = 20; //ms * volumeValue
uint8_t volumeSleepFadeOutTime = 50;

unsigned long scrollingStationStringTime;  // Czas do odswiezania scorllingu
uint8_t scrollingRefresh = 50;              // Czas w ms przewijania tekstu funkcji Scroller

uint8_t vuMeterRefreshCounterSet = 0;      // Mnoznik co ile petli loopRefreshTime ma byc odswiezony VU Meter
uint8_t scrollerRefreshCounterSet = 0;     // Mnoznik co ile petli loopRefreshTime ma byc odswiezony i przewiniety o 1px Scroller

uint16_t stationStringScrollWidth;         // szerokosc Stringu nazwy stacji w funkcji Scrollera
uint16_t xPositionStationString = 0;       // Pozycja początkowa dla przewijania tekstu StationString
uint16_t offset;                           // Zminnna offsetu dla funkcji Scrollera - przewijania streamtitle na ekranie OLED
unsigned char * psramData;                 // zmienna do trzymania danych stacji w pamieci PSRAM

unsigned long vuMeterMilisTimeUpdate;           // Zmienna przechowujaca czas dla funkci millis VU Meter refresh
uint8_t vuMeterRefreshTime = 50;                // Czas w ms odswiezania VUmetera

uint8_t wifiSignalLevel = 0;
uint8_t wifiSignalLevelLast = 7;          // Pamiecm poprzedniego stanu signalLevel

// ---- Serwer Web ---- //
unsigned long currentTime = millis();
unsigned long previousTime = 0;
const long timeoutTime = 2000;
bool urlToPlay = false;   // Flaga czy mamy uruchomic stream przekazany przez strone www
bool urlPlaying = false; // Flaga czy gramy z adresu URL ze strony www


// ---- Sprawdzenie funkcji pilota, zminnne do pomiaru róznicy czasów ---- //
unsigned long runTime = 0;
unsigned long runTime1 = 0;
unsigned long runTime2 = 0;


String stationStringScroll = "";     // Zmienna przechowująca tekst do przewijania na ekranie
String stationName;                  // Nazwa aktualnie wybranej stacji radiowej
String stationString;                // Dodatkowe dane stacji radiowej (jeśli istnieją)
String stationStringWeb;                // Dodatkowe dane stacji radiowej (jeśli istnieją)
String bitrateString;                // Zmienna przechowująca informację o bitrate
String sampleRateString;             // Zmienna przechowująca informację o sample rate
String bitsPerSampleString;          // Zmienna przechowująca informację o liczbie bitów na próbkę
String currentIP;
String stationNameStream;           // Nazwa stacji wyciągnieta z danych wysylanych przez stream
String streamCodec;
String stationLogoUrl;
String timezone;


String header;                      // Zmienna dla serwera www
String sliderValue = "0";
String url2play = "";


File myFile;  // Uchwyt pliku

//U8G2_SSD1322_NHD_256X64_F_4W_HW_SPI u8g2(U8G2_R2, /* cs=*/CS_OLED, /* dc=*/DC_OLED, /* reset=*/RESET_OLED);  // Hardware SPI 3.12inch OLED
//U8G2_SSD1309_128X64_NONAME0_F_4W_HW_SPI u8g2(U8G2_R2, /* cs=*/CS_OLED, /* dc=*/DC_OLED, /* reset=*/RESET_OLED);  
//U8G2_SH1122_256X64_F_4W_HW_SPI u8g2(U8G2_R2, /* cs=*/ CS_OLED, /* dc=*/ DC_OLED, /* reset=*/ RESET_OLED);		// Hardware SPI  2.08inch OLED
//U8G2_SSD1363_256X128_F_4W_HW_SPI u8g2(U8G2_R0, /* cs=*/CS_OLED, /* dc=*/DC_OLED, /* reset=*/RESET_OLED);  // Hardware SPI 3.12inch OLED

#if defined(SSD1322)
  U8G2_SSD1322_NHD_256X64_F_4W_HW_SPI u8g2(U8G2_R2, CS_OLED, DC_OLED, RESET_OLED);
#elif defined(SSD1309)
  U8G2_SSD1309_128X64_NONAME0_F_4W_HW_SPI u8g2(U8G2_R2, CS_OLED, DC_OLED, RESET_OLED);
#elif defined(SH1122)
  U8G2_SH1122_256X64_F_4W_HW_SPI u8g2(U8G2_R2, CS_OLED, DC_OLED, RESET_OLED);
#elif defined(SSD1363) 
  U8G2_SSD1363_256X128_F_4W_HW_SPI u8g2(U8G2_R0, CS_OLED, DC_OLED, RESET_OLED);
#elif defined(SSD1306)   
  U8G2_SSD1306_128X64_NONAME_F_4W_HW_SPI u8g2(U8G2_R0, CS_OLED, DC_OLED, RESET_OLED);
#else
  #error "Nie wybrano typu wyswietlacza!"
#endif


// Przypisujemy port serwera www
AsyncWebServer server(80);
AsyncWebSocket ws("/ws"); //Start obsługi Websocketów


// Inicjalizacja WiFiManagera
WiFiManager wifiManager;


// Konfiguracja nowego SPI z wybranymi pinami dla czytnika kart SD
SPIClass customSPI = SPIClass(HSPI);  // Używamy HSPI, ale z własnymi pinami

#ifdef twoEncoders
  ezButton button1(SW_PIN1);  // Utworzenie obiektu przycisku z enkodera 2 ezButton
#endif

ezButton button2(SW_PIN2);  // Utworzenie obiektu przycisku z enkodera 2 ezButton
Audio audio;                // Obiekt do obsługi funkcji związanych z dźwiękiem i audio

Ticker timer1;             // Timer do aktualizacji Zegara
Ticker timer2;             // Timer funkcji Dimmer
Ticker timer3;             // Timer dla funkcji Sleep
Ticker timer4;             // Timer startu migania LED
//Ticker timer5;             // Timer probkowania klawiatury ADC
WiFiClient client;         // Obiekt do obsługi połączenia WiFi dla klienta HTTP


// ------------------- STRON HTML zaszyte w kodzie -------------------
const char stylehead_html[] PROGMEM = R"rawliteral(
  <!DOCTYPE HTML><html>
  <head>
    <link rel='icon' href='/favicon.ico' type='image/x-icon'>
    <link rel="shortcut icon" href="/favicon.ico" type="image/x-icon">
    <link rel="apple-touch-icon" sizes="180x180" href="/icon.png">
    <link rel="icon" type="image/png" sizes="192x192" href="/icon.png">

    <meta name="viewport" content="width=device-width, initial-scale=1">
    <title>Evo Web Radio</title>
    <style>
      html {font-family: Arial; display: inline-block; text-align: center;}
      h2 {font-size: 1.3rem;}
      p {font-size: 0.95rem;}
      table {border: 1px solid black; border-collapse: collapse; margin: 0px 0px;}
      td, th {font-size: 0.8rem; border: 1px solid gray; border-collapse: collapse;}
      td:hover {font-weight:bold;}
      a {color: black; text-decoration: none;}
      body {max-width: 1380px; margin:0px auto; padding-bottom: 25px; background: #D0D0D0;}
      .slider {-webkit-appearance: none; margin: 14px; width: 330px; height: 10px; background: #4CAF50; outline: none; -webkit-transition: .2s; transition: opacity .2s; border-radius: 5px;}
      .slider::-webkit-slider-thumb {-webkit-appearance: none; appearance: none; width: 35px; height: 25px; background: #4a4a4a; cursor: pointer; border-radius: 5px;}
      .slider::-moz-range-thumb { width: 35px; height: 35px; background: #4a4a4a; cursor: pointer; border-radius: 5px;} 
      .button { background-color: #4CAF50; border: 1; color: white; padding: 10px 20px; border-radius: 5px;}
      .buttonBank { background-color: #4CAF50; border: 1; color: white; padding: 8px 8px; border-radius: 5px; width: 35px; height: 35px; margin: 0 1.5px;}
      .buttonBankSelected { background-color: #505050; border: 1; color: white; padding: 8px 8px; border-radius: 5px; width: 35px; height: 35px; margin: 0 1.5px;}
      .buttonBank:active {background-color: #4a4a4a; box-shadow: 0 4px #666; transform: translateY(2px);}
      .buttonBank:hover {background-color: #4a4a4a;}
      .button:hover {background-color: #4a4a4a;}
      .button:active {background-color: #4a4a4a; box-shadow: 0 4px #666; transform: translateY(2px);}
      .column {padding: 5px; display: flex; justify-content: space-between;}
      .columnlist {padding: 10px; display: flex; justify-content: center;}
      .stationList {text-align:left; margin-top: 0px; width: 280px; margin-bottom:0px;cursor: pointer;}
      .stationNumberList {text-align:center; margin-top: 0px; width: 35px; margin-bottom:0px;}
      .stationListSelected {text-align:left; margin-top: 0px; width: 280px; margin-bottom:0px;cursor: pointer; background-color: #4CAF50;}
      .stationNumberListSelected {text-align:center; margin-top: 0px; width: 35px; margin-bottom:0px; background-color: #4CAF50;}
      .station-name {}  
    </style>
  </head>
)rawliteral";

const char index_html[] PROGMEM = R"rawliteral(
  <!DOCTYPE HTML><html>
  <head>
    <link rel='icon' href='/favicon.ico' type='image/x-icon'>
    <link rel="shortcut icon" href="/favicon.ico" type="image/x-icon">
    <link rel="apple-touch-icon" sizes="180x180" href="/icon.png">
    <link rel="icon" type="image/png" sizes="192x192" href="/icon.png">

    <meta name="viewport" content="width=device-width, initial-scale=1">
    <title>Evo Web Radio</title>
    <style>
      html {font-family: Arial; display: inline-block; text-align: center;}
      h2 {font-size: 1.3rem;}
      p {font-size: 0.95rem;}
      table {border: 1px solid black; border-collapse: collapse; margin: 0px 0px;}
      td, th {font-size: 0.8rem; border: 1px solid gray; border-collapse: collapse;}
      td:hover {font-weight:bold;}
      a {color: black; text-decoration: none;}
      body {max-width: 1380px; margin:0px auto; padding-bottom: 25px; background: #D0D0D0;}
      .slider {-webkit-appearance: none; margin: 14px; width: 330px; height: 10px; background: #4CAF50; outline: none; -webkit-transition: .2s; transition: opacity .2s; border-radius: 5px;}
      .slider::-webkit-slider-thumb {-webkit-appearance: none; appearance: none; width: 35px; height: 25px; background: #4a4a4a; cursor: pointer; border-radius: 5px;}
      .slider::-moz-range-thumb { width: 35px; height: 35px; background: #4a4a4a; cursor: pointer; border-radius: 5px;} 
      .button { background-color: #4CAF50; border: 1; color: white; padding: 10px 20px; border-radius: 5px;}
      .buttonBank { background-color: #4CAF50; border: 1; color: white; padding: 8px 8px; border-radius: 5px; width: 35px; height: 35px; margin: 0 1.5px;}
      .buttonBankSelected { background-color: #505050; border: 1; color: white; padding: 8px 8px; border-radius: 5px; width: 35px; height: 35px; margin: 0 1.5px;}
      .buttonBank:active {background-color: #4a4a4a box-shadow: 0 4px #666; transform: translateY(2px);}
      .buttonBank:hover {background-color: #4a4a4a;}
      .button:hover {background-color: #4a4a4a;}
      .button:active {background-color: #4a4a4a; box-shadow: 0 4px #666; transform: translateY(2px);}
      .column { align: center; padding: 5px; display: flex; justify-content: space-between;}
      .columnlist { align: center; padding: 10px; display: flex; justify-content: center;}
      .stationList {text-align:left; margin-top: 2px; width: 280px; height:18px; margin-bottom:0px;cursor: pointer;}
      .stationNumberList {text-align:center; margin-top: 2px; width: 35px; height:18px; margin-bottom:0px;}
      .stationListSelected {text-align:left; margin-top: 2px; width: 280px; height:18px; margin-bottom:0px;cursor: pointer; background-color: #4CAF50;}
      .stationNumberListSelected {text-align:center; margin-top: 2px; width: 35px; height:18px; margin-bottom:0px; background-color: #4CAF50;} 
      .wifi-wrapper {display: flex; align-items: flex-end; gap: 1px; height: 13px; margin-top: -3px; margin-bottom: 3px; justify-content: center; }
      .wifiBar {width: 2px;background-color: #555; border-radius: 2px; transition: background-color 0.2s;}
      .bar1 { height: 2px; }
      .bar2 { height: 4px; }
      .bar3 { height: 6px; }
      .bar4 { height: 8px; }
      .bar5 { height: 10px; }
      .bar6 { height: 12px; }
    </style>
  </head>

  <body>
    <h2>Evo Web Radio</h2>
  
    <div id="display" style="display: inline-block; padding: 6px; border: 2px solid #4CAF50; border-radius: 15px; background-color: #4a4a4a; font-size: 1.45rem; 
      color: #AAA; width: 345px; text-align: center; white-space: nowrap; box-shadow: 0 0 20px #4CAF50;" onClick="flashBackground(); displayMode()">
      
      <div style="margin-bottom: 10px; font-weight: bold; overflow: hidden; text-overflow: ellipsis; -webkit-text-stroke: 0.3px black; text-stroke: 0.3px black;">
        <span id="textStationName"><b>STATIONNAME</b></span>
      </div>
      
      <div style="width: 345px; margin-bottom: 10px;">
        <div id="stationTextDiv" style="display: block; text-overflow: ellipsis; white-space: normal; font-size: 1.0rem; color: #999; margin-bottom: 10px; text-align: center; align-items: center; height: 4.2em; justify-content: center; overflow: hidden; line-height: 1.4em;">
          <span id="stationText">STATIONTEXT</span>
        </div>
        <div id="muteIndicatorDiv" style="text-align:center; color:#4CAF50; font-weight:bold; font-size:1.0rem; height:1.4em; margin-top:-5px;">
        <span id="muteIndicator"></span>
        </div>
      </div>
      
      <div style="height: 1px; background-color: #4CAF50; margin: 5px 0;"></div>

      
      <div style="display: flex; justify-content: center; gap: 13px; font-size: 1.00rem; color: #999;">
        <div><span id="bankValue">Bank: --</span></div>
          <div style="display: flex; justify-content: center; gap: 6px; font-size: 0.55rem; color: #999;margin: 4px 0;">
            <div><span id="samplerate">---.-kHz</span></div>
            <div><span id="bitrate">---kbps</span></div>
            <div><span id="bitpersample">---bit</span></div>
            <div><span id="streamformat">----</span></div>
            WiFi: <div class="wifi-wrapper">
            <div class="wifiBar bar1" id="wifiBar1"></div>
            <div class="wifiBar bar2" id="wifiBar2"></div>
            <div class="wifiBar bar3" id="wifiBar3"></div>
            <div class="wifiBar bar4" id="wifiBar4"></div>
            <div class="wifiBar bar5" id="wifiBar5"></div>
            <div class="wifiBar bar6" id="wifiBar6"></div>
  	      </div>
        </div>
        <div><span id="stationNumber">Station: --</span></div>
      </div>

  </div>
  <br>
  <br>
  <script>

  var websocket;

  function updateSliderVolume(element) 
  {
    var sliderValue = document.getElementById("volumeSlider").value;
    document.getElementById("textSliderValue").innerText = sliderValue;

    if (websocket && websocket.readyState === WebSocket.OPEN) 
    {
      websocket.send("volume:" + sliderValue);
    } 
    else 
    {
      console.warn("WebSocket niepołączony");
    }
  }

  function changeStation(number) 
  {
    if (websocket.readyState === WebSocket.OPEN) 
    {
      websocket.send("station:" + number);
    } 
    else 
    {
      console.log("WebSocket nie jest otwarty");
    }
  }

  function changeBank(number) 
  {
    if (websocket.readyState === WebSocket.OPEN) 
    {
      websocket.send("bank:" + number);
    } 
    else 
    {
      console.log("WebSocket nie jest otwarty");
    }
  }


  function displayMode() 
  {
    //fetch("/displayMode")
    if (websocket.readyState === WebSocket.OPEN) 
    {
      websocket.send("displayMode");
    } 
    else 
    {
      console.log("WebSocket nie jest otwarty");
    }
  }
  
  function setWifi(level) 
  {
    for (let i = 1; i <= 6; i++) 
    {
      const bar = document.getElementById("wifiBar" + i);
      if (bar) {bar.style.backgroundColor = (i <= level) ? "#4CAF50" : "#555";}
    }
  }


  function connectWebSocket() 
  {
    websocket = new WebSocket('ws://' + window.location.hostname + '/ws');
    websocket.onopen = function () 
    {
      console.log("WebSocket polaczony");
    };
    
    websocket.onclose = function (event) 
    {
      console.log("WebSocket zamkniety. Proba ponownego polaczenia za 3 sekundy...");
      setTimeout(connectWebSocket, 3000); // próba ponownego połączenia
    };

    websocket.onerror = function (error) 
    {
      console.error("Blad WebSocket: ", error);
      websocket.close(); // zamyka połączenie, by wywołać reconnect
    };
    
    websocket.onmessage = function(event) 
    {
      if (event.data === "reload") 
      {
        location.reload();
      }  
      
      if (event.data.startsWith("volume:")) 
      {
        var vol = parseInt(event.data.split(":")[1]);
        document.getElementById("volumeSlider").value = vol;
        document.getElementById("textSliderValue").innerText = vol;
      }
      
      if (event.data.startsWith("station:")) 
      {
        var station = parseInt(event.data.split(":")[1]);
        highlightStation(station);
        //document.getElementById('stationNumber').innerText = event.data.split(':')[1];
        document.getElementById('stationNumber').innerText ='Station: ' + station; 
      }
      
      if (event.data.startsWith("stationname:")) 
      {
        var value = event.data.split(":")[1];
        document.getElementById("textStationName").innerHTML = `<b>${value}</b>`;
        //checkStationTextLength();
      }  

      if (event.data.startsWith("stationtext$")) 
      {
        //var stationtext = event.data.split("$")[1];
        //document.getElementById("stationText").innerHTML = `${stationtext}`;
        
        var stationtext = event.data.substring(event.data.indexOf("$") + 1);
        //document.getElementById("stationText").innerHTML = stationtext;       
        document.getElementById("stationText").textContent = stationtext;
      }  

      if (event.data.startsWith("bank:")) 
      {
        var bankValue = parseInt(event.data.split(":")[1]);
        document.getElementById('bankValue').innerText = 'Bank: ' + bankValue;
      } 

      //if (event.data.startsWith("samplerate:")) 
      //{
      //  var samplerate = parseInt(event.data.split(":")[1]);
      //  var formattedRate = (samplerate / 1000).toFixed(1) + "kHz";
      //  document.getElementById('samplerate').innerText = formattedRate;
      //}
      
      if (event.data.startsWith("samplerate:")) 
      {
        var raw = event.data.split(":")[1];
        var samplerate = parseInt(raw);

        if (isNaN(samplerate)) 
        {
          document.getElementById('samplerate').innerText = '---.-kHz';
        } 
        else 
        {
          var formattedRate = (samplerate / 1000).toFixed(1) + "kHz";
          document.getElementById('samplerate').innerText = formattedRate;
        }
      }

      //if (event.data.startsWith("bitrate:")) 
      //{	
      //  var bitrate = parseInt(event.data.split(":")[1]);
      //  document.getElementById('bitrate').innerText = bitrate + 'kbps';
      //}

      if (event.data.startsWith("bitrate:")) 
      {	
        var raw = event.data.split(":")[1];
        var bitrate = parseInt(raw);

        if (isNaN(bitrate)) 
        {
          document.getElementById('bitrate').innerText = '---kbps';
        } 
        else 
        {
          document.getElementById('bitrate').innerText = bitrate + 'kbps';
        }
      }

      
      //if (event.data.startsWith("bitpersample:")) 
      //{	
      //  var bitpersample = parseInt(event.data.split(":")[1]);
      //  document.getElementById('bitpersample').innerText = bitpersample + 'bit';
      //}

      if (event.data.startsWith("bitpersample:")) 
      {	
        var raw = event.data.split(":")[1];
        var bitpersample = parseInt(raw);

        if (isNaN(bitpersample)) 
        {
          document.getElementById('bitpersample').innerText = '---bit';
        } 
        else 
        {
          document.getElementById('bitpersample').innerText = bitpersample + 'bit';
        }
      }

      
      if (event.data.startsWith("streamformat:")) 
      {	
        var streamformat = event.data.split(":")[1];
        document.getElementById('streamformat').innerText = streamformat;
      }  

      if (event.data.startsWith("mute:")) 
      {
        //var muteInd = parseInt(event.data.split(":")[1]);
        const muteInd = event.data.split(":")[1] === "1" ? 1 : 0;
        document.getElementById('muteIndicator').textContent = (muteInd === 1) ? 'MUTED' : '';       
      }

      if (event.data.startsWith("wifi:")) 
      {
        const level = parseInt(event.data.split(":")[1]);
        if (!isNaN(level)) {setWifi(Math.min(Math.max(level, 1), 6));}
      }


    }

  };
  
  function highlightStation(stationId) 
  {
    // Usuń poprzednie zaznaczenia
    document.querySelectorAll(".stationList").forEach(el => {
    el.classList.remove("stationListSelected");
    //el.innerHTML = el.dataset.stationName || el.innerText; // przywróć oryginalny numer
    el.innerText = el.dataset.stationName || el.innerText;


    });

    document.querySelectorAll(".stationNumberList").forEach(el => {
      el.classList.remove("stationNumberListSelected");
      el.innerHTML = el.dataset.stationNumber || el.innerText; // przywróć oryginalny numer
    });

    // Zaznacz nową stację
    const numCells = document.querySelectorAll(".stationNumberList");
    const stationCells = document.querySelectorAll(".stationList");

    const numCell = numCells[stationId - 1];
    const stationCell = stationCells[stationId - 1];

    if (numCell && stationCell) 
    {
      numCell.classList.add("stationNumberListSelected");
      stationCell.classList.add("stationListSelected");
      
      // Pogrub nazwę stacji
      stationCell.dataset.stationName = stationCell.innerText; // zapisz oryginalny tekst
      stationCell.innerHTML = `<b>${stationCell.innerText}</b>`; // pogrubienie nazwy stacji

      //const original = stationCell.dataset.originalName || stationCell.innerText;
      //stationCell.dataset.originalName = original;
      //stationCell.innerText = original;
      //stationCell.style.fontWeight = "bold";

        
      // Pogrub numer
      numCell.dataset.stationNumber = numCell.innerText; // zapisz oryginalny numer
      numCell.innerHTML = `<b>${numCell.innerText}</b>`; 
      //const originalNum = numCell.dataset.originalNumber || numCell.innerText;
      //numCell.dataset.originalNumber = originalNum;
      //numCell.innerText = originalNum;
      //numCell.style.fontWeight = "bold";


    }
  }
  
  function flashBackground() 
	{
	  const div = document.getElementById('display');
	  const originalColor = div.style.backgroundColor;

	  const textSpan = document.getElementById('textStationName');
    const originalText = textSpan.innerText;


	  div.style.backgroundColor = '#115522'; // kolor flash
	  //textSpan.innerText = 'OLED Display Mode Changed';
    textSpan.innerHTML = '<b>Display Mode Changed</b>';  

	  setTimeout(() => 
	  {
		  div.style.backgroundColor = originalColor;
		  //textSpan.innerText = originalText;
      textSpan.innerHTML = `<b>${originalText}</b>`;
	  }, 150); // czas w ms flasha
	}


  document.addEventListener("DOMContentLoaded", function () 
  {
    connectWebSocket(); // podlaczamy websockety

    const slider = document.getElementById("volumeSlider");
    slider.addEventListener("wheel", function (event) 
    {
      event.preventDefault(); // zapobiega przewijaniu strony

      let currentValue = parseInt(slider.value);
      const step = parseInt(slider.step) || 1;
      const max = parseInt(slider.max);
      const min = parseInt(slider.min);

      if (event.deltaY < 0) {
        // przewijanie w górę (zwiększ)
        slider.value = Math.min(currentValue + step, max);
      } else {
        // przewijanie w dół (zmniejsz)
        slider.value = Math.max(currentValue - step, min);
      }

      updateSliderVolume(slider); // wywołaj aktualizację
    });
  });

  window.onpageshow = function(event) 
  {
    if (event.persisted) 
    {
      window.location.reload();
    }
  };

 </script>
)rawliteral";

const char list_html[] PROGMEM = R"rawliteral(
  <!DOCTYPE HTML><html>
  <head>
    <link rel='icon' href='/favicon.ico' type='image/x-icon'>
    <link rel="shortcut icon" href="/favicon.ico" type="image/x-icon">
    <link rel="apple-touch-icon" sizes="180x180" href="/icon.png">
    <link rel="icon" type="image/png" sizes="192x192" href="/icon.png">

    <meta name="viewport" content="width=device-width, initial-scale=1">
    <title>Evo Web Radio</title>
    <style>
      html {font-family: Arial; display: inline-block; text-align: center;}
      h2 {font-size: 1.3rem;}
      p {font-size: 1.1rem;}
      table {border: 1px solid black; border-collapse: collapse; margin: 0px 0px;}
      td, th {font-size: 0.8rem; border: 1px solid gray; border-collapse: collapse;}
      td:hover {font-weight:bold;}
      a {color: black; text-decoration: none;}
      body {max-width: 1380px; margin:0px auto; padding-bottom: 25px;}
      .columnlist { align: center; padding: 10px; display: flex; justify-content: center;}
    </style>
  </head>
)rawliteral";

const char config_html[] PROGMEM = R"rawliteral(
  <!DOCTYPE HTML>
  <html>
  <head>
    <link rel='icon' href='/favicon.ico' type='image/x-icon'>
    <link rel="shortcut icon" href="/favicon.ico" type="image/x-icon">
    <link rel="apple-touch-icon" sizes="180x180" href="/icon.png">
    <link rel="icon" type="image/png" sizes="192x192" href="/icon.png">

    <meta name="viewport" content="width=device-width, initial-scale=1">
    <title>Evo Web Radio</title>
    <style>
      html {font-family: Arial; display: inline-block; text-align: center;}
      h1 {font-size: 2.3rem;}
      h2 {font-size: 1.3rem;}
      table {border: 1px solid black; border-collapse: collapse; margin: 20px auto; width: 80%;}
      th, td {font-size: 1rem; border: 1px solid gray; padding: 8px; text-align: left;}
      td:hover {font-weight: bold;}
      a {color: black; text-decoration: none;}
      body {max-width: 1380px; margin:0 auto; padding-bottom: 25px;}
      .tableSettings {border: 2px solid #4CAF50; border-collapse: collapse; margin: 10px auto; width: 60%;}
      input[type="checkbox"] {accent-color: #66BB6A; color: #FFFF50; width: 13px; height: 13px; }
      input[type="text"] { width: 60px; box-sizing: border-box;}
      @media (max-width:768px){.about-box,.tableSettings{width:90%!important;} table{width:100%!important;} th,td{font-size:0.9rem;}}
    </style>
    </head>

  <body>
  <h2>Evo Web Radio - Settings</h2>
  <form action="/configupdate" method="POST">
  <table class="tableSettings">
  <tr><th>Display Setting</th><th>Value</th></tr>
  <tr><td>Normal Display Brightness (0-255), default:180</td><td><input type="number" name="displayBrightness" min="1" max="255" value="%D1"></td></tr>
  <tr><td>Dimmed Display Brightness (0-200), default:20</td><td><input type="number" name="dimmerDisplayBrightness" min="1" max="200" value="%D2"></td></tr>
  <tr><td>Dimmed Display Brightness in Sleep Mode (0-50), default:1</td><td><input type="number" name="dimmerSleepDisplayBrightness" min="1" max="50" value="%D12"></td></tr>
  <tr><td>Auto Dimmer Delay Time (1-255 sec.), default:5</td><td><input type="number" name="displayAutoDimmerTime" min="1" max="255" value="%D3"></td></tr>
  <tr><td>Auto Dimmer, default:On</td><td><input type="checkbox" name="displayAutoDimmerOn" value="1" %S1_checked></td></tr>
  <tr><td>OLED Display Clock in Sleep Mode default:Off</td><td><input type="checkbox" name="f_displayPowerOffClock" value="1" %S19_checked></td></tr>
  <tr><td>OLED Display Power Save Mode, default:Off</td><td><input type="checkbox" name="displayPowerSaveEnabled" value="1" %S9_checked></td></tr>
  <tr><td>OLED Display Power Save Time (1-600sek.), default:20</td><td><input type="number" name="displayPowerSaveTime" min="1" max="600" value="%D9"></td></tr>
  <tr><td>OLED Display Mode - 0-Radio basic, 1-Clock, 2-Three lines, 3-Centered, 4-VU analog, 5-VU digital</td><td><input type="number" name="displayMode" min="0" max="5" value="%D6"></td></tr>

  <tr><th>Other Setting</th><th></th></tr>
  <tr><td>Time Voice Info Every Hour, default:On</td><td><input type="checkbox" name="timeVoiceInfoEveryHour" value="1" %S3_checked></td></tr>
  <tr><td>Encoder Function Order (0-1), 0-Volume, click for station list, 1-Station list, click for Volume</td><td><input type="number" name="encoderFunctionOrder" min="0" max="1" value="%D5"></td></tr>
  <tr><td>Radio Scroller & VU Meter Refresh Time (15-100ms), default:50</td><td><input type="number" name="scrollingRefresh" min="15" max="100" value="%D8"></td></tr>
  <tr><td>ADC Keyboard Enabled, default:Off</td><td><input type="checkbox" name="adcKeyboardEnabled" value="1" %S7_checked></td></tr>
  <tr><td>Volume Steps 1-21 [Off], 1-42 [On], default:Off</td><td><input type="checkbox" name="maxVolumeExt" value="1" %S11_checked></td></tr>
  <tr><td>Station Name Read From Stream [On-From Stream, Off-From Bank] EXPERIMENTAL</td><td><input type="checkbox" name="stationNameFromStream" value="1" %S17_checked></td></tr>
  <tr><td>Radio switch to Standby After Power Fail, default:On</td><td><input type="checkbox" name="f_sleepAfterPowerFail" value="1" %S21_checked></td></tr>
  <tr><td>Volume Fade on Station Change and Power Off, default:Off</td><td><input type="checkbox" name="f_volumeFadeOn" value="1" %S22_checked></td></tr>
  <tr><td>Save ALWAYS Station No., Bank No., Volume, default:Off</td><td><input type="checkbox" name="f_saveVolumeStationAlways" value="1" %S23_checked></td></tr>
  <tr><td>Power Off Animation, default:Off</td><td><input type="checkbox" name="f_powerOffAnimation" value="1" %S24_checked></td></tr>
  <tr><td>Timezone Settings</td><td><button type="button" class="button" onclick="location.href='/timezone'">Set</button></td></tr>
  <tr><td>Remote Control Settings</td><td><button type="button" class="button" onclick="location.href='/remoteconfig'">Set</button></td></tr>
  <tr><td>Presets On (Key 0-9 switching stations 1 to 10), default:Off</td><td><input type="checkbox" name="f_Presets" value="1" %S25_checked></td></tr>
  <tr><td>Change station from list without click, default:Off</td><td><input type="checkbox" name="f_changeStationWithoutEncoderClick" value="1" %S26_checked></td></tr>


  <tr><th><b>VU Meter Settings</b></th></tr>
  <tr><td>VU Meter Mode (0-1), 0-dashed lines, 1-continuous lines</td><td><input type="number" name="vuMeterMode" min="0" max="1" value="%D4"></td></tr>
  <tr><td>VU Meter Visible (Mode 0, 3 only), default:On</td><td><input type="checkbox" name="vuMeterOn" value="1" %S5_checked></td></tr>
  <tr><td>VU Meter Peak & Hold Function, default:On</td><td><input type="checkbox" name="vuPeakHoldOn" value="1" %S13_checked></td></tr>
  <tr><td>VU Meter Smooth Function, default:On</td><td><input type="checkbox" name="vuSmooth" value="1" %S15_checked></td></tr>
  <tr><td>VU Meter Smooth Rise Speed [1 low - 32 High], default:24</td><td><input type="number" name="vuRiseSpeed" min="1" max="32" value="%D10"></td></tr>
  <tr><td>VU Meter Smooth Fall Speed [1 low - 32 High], default:6</td><td><input type="number" name="vuFallSpeed" min="1" max="32" value="%D11"></td></tr>
  </table>
  <input type="submit" value="Update">
  </form>


  <p style='font-size: 0.8rem;'><a href='/menu'>Go Back</a></p>
  </body>
  </html>
)rawliteral";

const char remoteconfig_html[] PROGMEM = R"rawliteral(
  <!DOCTYPE HTML>
  <html>
  <head>
  <meta charset="UTF-8">
  <meta name="viewport" content="width=device-width, initial-scale=1">
  <title>Evo Web Radio</title>

  <link rel="icon" href="/favicon.ico" type="image/x-icon">
  <link rel="shortcut icon" href="/favicon.ico" type="image/x-icon">
  <link rel="apple-touch-icon" sizes="180x180" href="/icon.png">
  <link rel="icon" type="image/png" sizes="192x192" href="/icon.png">

  <style>
  html{font-family:Arial;display:inline-block;text-align:center;}
  body{max-width:1380px;margin:0 auto;padding-bottom:25px;}
  h1{font-size:2.3rem;}h2{font-size:1.3rem;}
  table{border:1px solid #000;border-collapse:collapse;margin:20px auto;width:40%;}
  th,td{font-size:1rem;border:1px solid gray;padding:8px;text-align:left;}
  td:hover{font-weight:bold;}
  tr.selected{background:#d0f0d0;}
  a{color:black;text-decoration:none;}
  .tableSettings{border:2px solid #4CAF50;border-collapse:collapse;margin:5px auto;width:40%;}
  input[type="checkbox"]{accent-color:#66BB6A;color:#FFFF50;width:13px;height:13px;}
  input[type="text"]{width:70px;box-sizing:border-box;}
  #wsBox{border:2px solid #4CAF50;padding:10px;margin:15px auto;width:38%;background:#f5fff5;font-size:1.1rem;}
  #wsDetails{padding:5px;margin:5px auto;width:100%;background:#f5fff5;font-size:0.8rem;}
  p{font-size:0.7rem;}
  #AddrValue { margin-right: 10px; font-size:0.8rem;}
  #CmdValue { margin-right: 10px; font-size:0.8rem;}
  #Learn{background:#f5fff5;font-size:0.8rem; color:#4CAF50; font-weight:bold;}
  @media(max-width:768px){.about-box,.tableSettings,#wsBox{width:90%!important;}table{width:100%!important;}th,td{font-size:.9rem;}}
  </style>
  </head>

  <body>

  <h2>Evo Web Radio - Remote Control Config</h2>

  <div id="wsBox">
    <strong>Received code:</strong> <span id="codeValue">—</span>
    <div id="wsDetails">
      <p>Address:<span id="AddrValue">—</span>  Command:<span id="CmdValue">—</span></p>
    </div>
    <div id="Learn"><span id="LearnIndicator"></span></div>
  </div>

  <p></p>

  <div style="margin:10px;">
    <button onclick="toggleRemoteConfig()">Learning Mode - ON/OFF</button>
    <label><input type="checkbox" id="autoMode">AUTO Mode</label>&nbsp;&nbsp;
    <button type="button" onclick="skipCurrent()">Skip Sellected</button>
  </div>

  <p> Single Mouse Click on Row - Select, Double Mouse Click - Reset Value (set 0xFEFE)</p>
  <p> Auto Mode, auto increment and select next cell affer receiving IR code</p>

  <form action="/remoteconfigupdate" method="POST">
  <table class="tableSettings">
  <tr><th>Codes:</th><th>Value</th></tr>

  <tr><td>Volume Up +</td><td><input type="text" name="cmdVolumeUp" value="%D0" pattern="0x[0-9A-Fa-f]{4}" maxlength="6" title="Format: 0xFFFF"></td></tr>
  <tr><td>Volume Down -</td><td><input type="text" name="cmdVolumeDown" value="%D1" pattern="0x[0-9A-Fa-f]{4}" maxlength="6" title="Format: 0xFFFF"></td></tr>
  <tr><td>Arrow Right (Next Station / Next Bank)</td><td><input type="text" name="cmdArrowRight" value="%D2" pattern="0x[0-9A-Fa-f]{4}" maxlength="6" title="Format: 0xFFFF"></td></tr>
  <tr><td>Arrow Left (Prev Station / Prev Bank)</td><td><input type="text" name="cmdArrowLeft" value="%D3" pattern="0x[0-9A-Fa-f]{4}" maxlength="6" title="Format: 0xFFFF"></td></tr>
  <tr><td>Arrow Up (Station List Up)</td><td><input type="text" name="cmdArrowUp" value="%D4" pattern="0x[0-9A-Fa-f]{4}" maxlength="6" title="Format: 0xFFFF"></td></tr>
  <tr><td>Arrow Down (Station List Down)</td><td><input type="text" name="cmdArrowDown" value="%D5" pattern="0x[0-9A-Fa-f]{4}" maxlength="6" title="Format: 0xFFFF"></td></tr>

  <tr><td>Back</td><td><input type="text" name="cmdBack" value="%D6" pattern="0x[0-9A-Fa-f]{4}" maxlength="6" title="Format: 0xFFFF"></td></tr>
  <tr><td>OK / Enter</td><td><input type="text" name="cmdOk" value="%D7" pattern="0x[0-9A-Fa-f]{4}" maxlength="6" title="Format: 0xFFFF"></td></tr>

  <tr><td>Display Screen Mode</td><td><input type="text" name="cmdSrc" value="%D8" pattern="0x[0-9A-Fa-f]{4}" maxlength="6" title="Format: 0xFFFF"></td></tr>
  <tr><td>Mute</td><td><input type="text" name="cmdMute" value="%D9" pattern="0x[0-9A-Fa-f]{4}" maxlength="6" title="Format: 0xFFFF"></td></tr>
  <tr><td>Equalizer</td><td><input type="text" name="cmdAud" value="%D10" pattern="0x[0-9A-Fa-f]{4}" maxlength="6" title="Format: 0xFFFF"></td></tr>

  <tr><td>Display Brightness / Bank Network Update</td><td><input type="text" name="cmdDirect" value="%D11" pattern="0x[0-9A-Fa-f]{4}" maxlength="6" title="Format: 0xFFFF"></td></tr>

  <tr><td>Bank Menu (-)</td><td><input type="text" name="cmdBankMinus" value="%D12" pattern="0x[0-9A-Fa-f]{4}" maxlength="6" title="Format: 0xFFFF"></td></tr>
  <tr><td>Bank Menu (+)</td><td><input type="text" name="cmdBankPlus" value="%D13" pattern="0x[0-9A-Fa-f]{4}" maxlength="6" title="Format: 0xFFFF"></td></tr>

  <tr><td>Power On / Off</td><td><input type="text" name="cmdRed" value="%D14" pattern="0x[0-9A-Fa-f]{4}" maxlength="6" title="Format: 0xFFFF"></td></tr>
  <tr><td>Sleep</td><td><input type="text" name="cmdGreen" value="%D15" pattern="0x[0-9A-Fa-f]{4}" maxlength="6" title="Format: 0xFFFF"></td></tr>

  <tr><td>Key 0</td><td><input type="text" name="cmdKey0" value="%D16" pattern="0x[0-9A-Fa-f]{4}" maxlength="6" title="Format: 0xFFFF"></td></tr>
  <tr><td>Key 1</td><td><input type="text" name="cmdKey1" value="%D17" pattern="0x[0-9A-Fa-f]{4}" maxlength="6" title="Format: 0xFFFF"></td></tr>
  <tr><td>Key 2</td><td><input type="text" name="cmdKey2" value="%D18" pattern="0x[0-9A-Fa-f]{4}" maxlength="6" title="Format: 0xFFFF"></td></tr>
  <tr><td>Key 3</td><td><input type="text" name="cmdKey3" value="%D19" pattern="0x[0-9A-Fa-f]{4}" maxlength="6" title="Format: 0xFFFF"></td></tr>
  <tr><td>Key 4</td><td><input type="text" name="cmdKey4" value="%D20" pattern="0x[0-9A-Fa-f]{4}" maxlength="6" title="Format: 0xFFFF"></td></tr>
  <tr><td>Key 5</td><td><input type="text" name="cmdKey5" value="%D21" pattern="0x[0-9A-Fa-f]{4}" maxlength="6" title="Format: 0xFFFF"></td></tr>
  <tr><td>Key 6</td><td><input type="text" name="cmdKey6" value="%D22" pattern="0x[0-9A-Fa-f]{4}" maxlength="6" title="Format: 0xFFFF"></td></tr>
  <tr><td>Key 7</td><td><input type="text" name="cmdKey7" value="%D23" pattern="0x[0-9A-Fa-f]{4}" maxlength="6" title="Format: 0xFFFF"></td></tr>
  <tr><td>Key 8</td><td><input type="text" name="cmdKey8" value="%D24" pattern="0x[0-9A-Fa-f]{4}" maxlength="6" title="Format: 0xFFFF"></td></tr>
  <tr><td>Key 9</td><td><input type="text" name="cmdKey9" value="%D25" pattern="0x[0-9A-Fa-f]{4}" maxlength="6" title="Format: 0xFFFF"></td></tr>

  </table>

  <input type="submit" value="Update">
  </form>

  <p style="font-size:.8rem;"><a href="/menu">Go Back</a></p>

  <script>
  let websocket;
  let activeInput = null;
  let inputs = [];
  let currentIndex = -1;
  let autoMode = false;

  function toggleRemoteConfig() {
    const xhr = new XMLHttpRequest();
    xhr.open("POST", "/toggleRemoteConfig", true);
    xhr.send();
  }

  function clearSelection() {
    document.querySelectorAll(".tableSettings tr")
      .forEach(r => r.classList.remove("selected"));
    activeInput = null;
    currentIndex = -1;
  }

  function selectInputByIndex(index) {
    if (index >= inputs.length) {
      autoMode = false;
      document.getElementById("autoMode").checked = false;
      clearSelection();
      return;
    }

    clearSelection();
    currentIndex = index;
    activeInput = inputs[index];
    const row = activeInput.closest("tr");
    row.classList.add("selected");
    activeInput.focus();
  }

  function moveNext() {
    selectInputByIndex(currentIndex + 1);
  }

  function skipCurrent() {
    if (!activeInput) return;
    activeInput.value = "0xFEFE";
    if (autoMode) moveNext();
  }

  document.getElementById("autoMode").addEventListener("change", function () {
    autoMode = this.checked;
    if (autoMode) selectInputByIndex(0);
    else clearSelection();
  });

  document.addEventListener("DOMContentLoaded", function () {
    inputs = Array.from(
      document.querySelectorAll('.tableSettings input[type="text"]')
    );

    inputs.forEach((input, index) => {
      const row = input.closest("tr");

      row.onclick = () => selectInputByIndex(index);
      row.ondblclick = () => {
        input.value = "0xFEFE";
        selectInputByIndex(index);
      };
    });

    websocket = new WebSocket('ws://' + window.location.hostname + '/ws');

    websocket.onmessage = function (event) {
      if (event.data.startsWith("addr:"))
        document.getElementById('AddrValue').innerText = event.data.split(":")[1];

      if (event.data.startsWith("cmd:"))
        document.getElementById('CmdValue').innerText = event.data.split(":")[1];

      if (event.data.startsWith("learn:"))
        document.getElementById("LearnIndicator").innerText =
          parseInt(event.data.split(":")[1]) ? "LEARNING MODE ON" : "";

      if (event.data.startsWith("ircode:")) {
        const codeStr = event.data.split(":")[1].trim();
        document.getElementById('codeValue').innerText = codeStr;

        if (activeInput) {
          activeInput.value = codeStr;
          if (autoMode) moveNext();
        }
      }
    };
  });
  </script>

  </body>
  </html>
)rawliteral";

const char adc_html[] PROGMEM = R"rawliteral(
  <!DOCTYPE HTML>
  <html>
  <head>
    <link rel='icon' href='/favicon.ico' type='image/x-icon'>
    <link rel="shortcut icon" href="/favicon.ico" type="image/x-icon">
    <link rel="apple-touch-icon" sizes="180x180" href="/icon.png">
    <link rel="icon" type="image/png" sizes="192x192" href="/icon.png">

    <meta name="viewport" content="width=device-width, initial-scale=1">
    <title>Evo Web Radio</title>
    <style>
      html {font-family: Arial; display: inline-block; text-align: center;}
      h1 {font-size: 2.3rem;}
      h2 {font-size: 1.3rem;}
      table {border: 1px solid black; border-collapse: collapse; margin: 10px auto; width: 40%;}
      th, td {font-size: 1rem; border: 1px solid gray; padding: 8px; text-align: left;}
      td:hover {font-weight: bold;}
      a {color: black; text-decoration: none;}
      body {max-width: 1380px; margin:0 auto; padding-bottom: 15px;}
      .tableSettings {border: 2px solid #4CAF50; border-collapse: collapse; margin: 10px auto; width: 40%;}
      .button { background-color: #4CAF50; border: 1; color: white; padding: 10px 20px; border-radius: 5px; width:200px;}
      .button:hover {background-color: #4a4a4a;}
      .button:active {background-color: #4a4a4a; box-shadow: 0 4px #666; transform: translateY(2px);}
    </style>
    </head>

  <body>
  <h2>Evo Web Radio - ADC Settings</h2>
  <form action="/configadc" method="POST">
  <table class="tableSettings">
  <tr><th>Button</th><th>Value</th></tr>
  <tr><td>Key 0</td><td><input type="number" name="keyboardButtonThreshold_0" min="0" max="4100" value="%D0"></td></tr>
  <tr><td>Key 1</td><td><input type="number" name="keyboardButtonThreshold_1" min="0" max="4100" value="%D1"></td></tr>
  <tr><td>Key 2</td><td><input type="number" name="keyboardButtonThreshold_2" min="0" max="4100" value="%D2"></td></tr>
  <tr><td>Key 3</td><td><input type="number" name="keyboardButtonThreshold_3" min="0" max="4100" value="%D3"></td></tr>
  <tr><td>Key 4</td><td><input type="number" name="keyboardButtonThreshold_4" min="0" max="4100" value="%D4"></td></tr>
  <tr><td>Key 5</td><td><input type="number" name="keyboardButtonThreshold_5" min="0" max="4100" value="%D5"></td></tr>
  <tr><td>Key 6</td><td><input type="number" name="keyboardButtonThreshold_6" min="0" max="4100" value="%D6"></td></tr>
  <tr><td>Key 7</td><td><input type="number" name="keyboardButtonThreshold_7" min="0" max="4100" value="%D7"></td></tr>
  <tr><td>Key 8</td><td><input type="number" name="keyboardButtonThreshold_8" min="0" max="4100" value="%D8"></td></tr>
  <tr><td>Key 9</td><td><input type="number" name="keyboardButtonThreshold_9" min="0" max="4100" value="%D9"></td></tr>
  <tr><td>OK / Enter Key</td><td><input type="number" name="keyboardButtonThreshold_Ok" min="0" max="4100" value="%D10"></td></tr>
  <tr><td>Display Bank Menu Key</td><td><input type="number" name="keyboardButtonThreshold_BankMenu" min="0" max="4100" value="%D11"></td></tr>
  <tr><td>Back Key</td><td><input type="number" name="keyboardButtonThreshold_Back" min="0" max="4100" value="%D12"></td></tr>
  <tr><td>OLED Display Mode Key</td><td><input type="number" name="keyboardButtonThreshold_DisplayMode" min="0" max="4100" value="%D13"></td></tr>
  <tr><td>Dimmer / Network Bank Update Key</td><td><input type="number" name="keyboardButtonThreshold_Dimmer" min="0" max="4100" value="%D14"></td></tr>
  <tr><td>Mute Key</td><td><input type="number" name="keyboardButtonThreshold_Mute" min="0" max="4100" value="%D15"></td></tr>
  
  <tr><td>Navigation Left - Previous Station / Bank</td><td><input type="number" name="keyboardButtonThreshold_ArrowLeft" min="0" max="4100" value="%D19"></td></tr>
  <tr><td>Navigation Right - Next Statition / Bank</td><td><input type="number" name="keyboardButtonThreshold_ArrowRight" min="0" max="4100" value="%D20"></td></tr>
  <tr><td>Navigation Up - Station List Up</td><td><input type="number" name="keyboardButtonThreshold_ArrowUp" min="0" max="4100" value="%D21"></td></tr>
  <tr><td>Navigation Down - Station List Down</td><td><input type="number" name="keyboardButtonThreshold_ArrowDown" min="0" max="4100" value="%D22"></td></tr>
  
  <tr><td>Presets On Key</td><td><input type="number" name="keyboardButtonThreshold_PresetsOn" min="0" max="4100" value="%D23"></td></tr>

  <tr><td>Keyboard Buttons Threshold Tolerance</td><td><input type="number" name="keyboardButtonThresholdTolerance" min="0" max="50" value="%D16"></td></tr>
  <tr><td>Keyboard Buttons Neutral</td><td><input type="number" name="keyboardButtonNeutral" min="0" max="4100" value="%D17"></td></tr>
  <tr><td>Keyboard Sample Delay (30-300ms)</td><td><input type="number" name="keyboardSampleDelay" min="30" max="300" value="%D18"></td></tr>
  </table>
  <input type="submit" value="ADC Thresholds Update">
  </form>
  <br>
  <button onclick="toggleAdcDebug()">ADC Debug ON/OFF</button>
  <script>
  function toggleAdcDebug() {
      const xhr = new XMLHttpRequest();
      xhr.open("POST", "/toggleAdcDebug", true);
      xhr.setRequestHeader("Content-Type", "application/x-www-form-urlencoded");
      xhr.onload = function() {
          if (xhr.status === 200) {
              alert("ADC Debug is now " + (xhr.responseText === "1" ? "ON" : "OFF"));
          } else {
              alert("Error: " + xhr.statusText);
          }
      };
      xhr.send(); // Wysyłanie pustego zapytania POST
  }
  </script>

  <p style='font-size: 0.8rem;'><a href='/menu'>Go Back</a></p>
  </body>
  </html>
)rawliteral";

const char menu_html[] PROGMEM = R"rawliteral(
  <!DOCTYPE HTML><html>
  <head>
  <link rel='icon' href='/favicon.ico' type='image/x-icon'>
  <link rel="shortcut icon" href="/favicon.ico" type="image/x-icon">
  <link rel="apple-touch-icon" sizes="180x180" href="/icon.png">
  <link rel="icon" type="image/png" sizes="192x192" href="/icon.png">

  <meta name="viewport" content="width=device-width, initial-scale=1">
  <title>Evo Web Radio</title>
  <style>
    html {font-family: Arial; display: inline-block; text-align: center;}
    h2 {font-size: 1.3rem;}
    p {font-size: 1.1rem;}
    a {color: black; text-decoration: none;}
    body {max-width: 1380px; margin:0px auto; padding-bottom: 25px;}
    .button { background-color: #4CAF50; border: 1; color: white; padding: 10px 20px; border-radius: 5px; width:200px;}
    .button:hover {background-color: #4a4a4a;}
    .button:active {background-color: #4a4a4a; box-shadow: 0 4px #666; transform: translateY(2px);}
    
  </style>
  </head>
  <body>
  <h2>Evo Web Radio - Menu</h2>
  <!-- <br><button class="button" onclick="location.href='/fwupdate'">OTA Update (Old)</button><br> -->
  <br><button class="button" onclick="location.href='/info'">Info</button><br>
  <br><button class="button" onclick="location.href='/ota'">OTA Update</button><br>
  <br><button class="button" onclick="location.href='/adc'">ADC Keyboard Settings</button><br>
  <br><button class="button" onclick="location.href='/list'">Storage Memory Explorer</button><br>
  <br><button class="button" onclick="location.href='/editor'">Memory Bank Editor</button><br>
  <br><button class="button" onclick="location.href='/browser'">Radio Browser API</button><br>
  <br><button class="button" onclick="location.href='/playurl'">Play from URL</button><br>
  <br><button class="button" onclick="location.href='/config'">Settings</button><br>
  <br><p style='font-size: 0.8rem;'><a href="#" onclick="window.location.replace('/')">Go Back</a></p>
  </body></html>

)rawliteral";

const char info_html[] PROGMEM = R"rawliteral(
  <!DOCTYPE HTML>
  <html>
  <head>
    <link rel='icon' href='/favicon.ico' type='image/x-icon'>
    <link rel="shortcut icon" href="/favicon.ico" type="image/x-icon">
    <link rel="apple-touch-icon" sizes="180x180" href="/icon.png">
    <link rel="icon" type="image/png" sizes="192x192" href="/icon.png">
    <meta name="viewport" content="width=device-width, initial-scale=1">
    <title>Evo Web Radio</title>
    <style>
      html{font-family:Arial;display:inline-block;text-align:center;} 
      h2{font-size:1.3rem;} 
      table{border:1px solid black;border-collapse:collapse;margin:10px auto;width:40%;} 
      th,td{font-size:1rem;border:1px solid gray;padding:8px;text-align:left;} 
      td:hover{font-weight:bold;} 
      a{color:black;text-decoration:none;} 
      body{max-width:1380px;margin:0 auto;padding-bottom:15px;} 
      .tableSettings{border:2px solid #4CAF50;border-collapse:collapse;margin:10px auto;width:40%;} 
      .signal-bars{display:inline-block;vertical-align:middle;margin-left:10px;} 
      .bar{display:inline-block;width:5px;margin-right:2px;background-color:#F2F2F2;height:10px;} 
      .bar.active{background-color:#4CAF50;} 
      .about-box{border:2px solid #4CAF50;border-collapse:collapse;margin:10px auto;width:40%;text-align:left;font-size:0.9rem;line-height:1.4rem;color:#222;} 
      .about-box h3{color:#2f7a2f;margin-top:0;text-align:center;font-size:1.05rem;} 
      .about-box a{color:#2b5bb3;text-decoration:none;} 
      .about-box a:hover{text-decoration:underline;}
      @media (max-width:768px){.about-box,.tableSettings{width:90%!important;} table{width:100%!important;} th,td{font-size:0.9rem;}}
    </style>
  </head>
  <body>
  <h2>Evo Web Radio - Info</h2>

  <div class="about-box">
    <h3>Project Info</h3>
    <p>This is a project of an Internet radio streamer called <strong>"Evo"</strong>. The hardware was built using an <strong>ESP32-S3</strong> microcontroller and a <strong>PCM5102A DAC codec</strong>.</p>
    <p>The design allows listening to various music stations from all around the world and works properly with streams encoded in <strong>MP3</strong>, <strong>AAC</strong>, 
    <strong>VORBIS</strong>, <strong>OPUS</strong>, and <strong>FLAC</strong> (up to 2000kbs, 24bit).</p>
    <p>All operations (volume control, station change, memory bank selection, power on/off) are handled via a single rotary encoder. It also supports infrared remote controls working on the <strong>NEC standard (38&nbsp;kHz)</strong>.</p>
    <p></p>
    <p>Source code and documentation are available at: <b><a href="https://github.com/dzikakuna/ESP32_radio_evo3" target="_blank">Link: https://github.com/dzikakuna/ESP32_radio_evo3</a></b></p>
    <p>Robgold 2026, Made in Poland</p>
  </div>

  <table class="tableSettings">
      <tr><td>ESP Serial Number:</td><td>%D0</td></tr>
      <tr>
        <td>Version:</td>
	      <td>
	        Firmware: %D1<br>
          ESP IDF:  %D8<br>
          ESP Core: %D9
	      </td>
      </tr>     
      <tr><td>Hostname:</td><td>%D2</td></tr>
      <tr><td>WiFi Signal Strength [dBm]:</td><td>%D3</td></tr>
      <tr><td>WiFi SSID:</td><td>%D4</td></tr>
      <tr><td>IP Address:</td><td>%D5</td></tr>
      <tr><td>MAC Address:</td><td>%D6</td></tr>
      <tr><td>Memory type:</td><td>%D7</td></tr>
    </table>
  <br>
  <p style="font-size:0.8rem;"><a href="/menu">Go Back</a></p>
  </body>
  </html>
)rawliteral";

const char urlplay_html[] PROGMEM = R"rawliteral(
  <!DOCTYPE HTML>
  <html>
    <head>
      <meta name="viewport" content="width=device-width, initial-scale=1">
      <title>Evo Web Radio</title>

      <style>
        html {font-family: Arial; text-align: center;}
        body {max-width: 1380px; margin: 0 auto; background: #D0D0D0; padding-bottom: 25px;}
        h2 {font-size: 1.3rem;}
        p {font-size: 0.95rem;}
        .slider{-webkit-appearance:none;margin:14px;width:330px;height:10px;background:#4CAF50;outline:none;-webkit-transition:.2s;transition:opacity .2s;border-radius:5px}
        .slider::-webkit-slider-thumb{-webkit-appearance:none;appearance:none;width:35px;height:25px;background:#4a4a4a;cursor:pointer;border-radius:5px}
        .slider::-moz-range-thumb{width:35px;height:35px;background:#4a4a4a;cursor:pointer;border-radius:5px}
        .button {background-color:#4CAF50;border:1; color:white; padding:10px 20px; border-radius:5px;cursor:pointer;}
        .button:hover {background-color:#4a4a4a;}
        .button.active {background-color: #115522; transform: scale(1.05); transition: all 0.15s ease;}
        #urlInput {width:350px; padding:5px; border-radius:5px; font-size:0.9rem;}
        #playBtn {padding:5px 10px; font-size:0.9rem;}
        #display {display:inline-block; padding:5px; border:2px solid #4CAF50; border-radius:15px; background-color:#4a4a4a; font-size:1.45rem; color:#AAA; width:345px; text-align:center; white-space:nowrap; box-shadow:0 0 20px #4CAF50;}
        #stationTextDiv {display:block; text-overflow:ellipsis; white-space:normal; font-size:1.0rem; color:#999; margin-bottom:10px; text-align:center; height:4.2em; overflow:hidden; line-height:1.4em;}
        #muteIndicatorDiv {text-align:center; color:#4CAF50; font-weight:bold; font-size:1.0rem; height:1.4em;}
        #urlInput.flash {background-color: #4CAF50;color: #fff; transition: background-color 0.3s ease;}
        .wifi-wrapper {display: flex; align-items: flex-end; gap: 1px; height: 13px; margin-top: -3px; margin-bottom: 3px; justify-content: center; }
        .wifiBar {width: 2px;background-color: #555; border-radius: 2px; transition: background-color 0.2s;}
        .bar1 { height: 2px; }
        .bar2 { height: 4px; }
        .bar3 { height: 6px; }
        .bar4 { height: 8px; }
        .bar5 { height: 10px; }
        .bar6 { height: 12px; }
      </style>
  </head>

  <body>
  <h2>Evo Web Radio - URL Play</h2>

  <div id="display" onclick="flashBackground(); displayMode();">
      <div style="margin-bottom:10px; font-weight:bold; overflow:hidden; text-overflow:ellipsis;">
          <span id="textStationName"><b>STATIONNAME</b></span>
      </div>

      <div style="width:345px; margin-bottom:10px;">
          <div id="stationTextDiv">
              <span id="stationText">STATIONTEXT</span>
          </div>
          <div id="muteIndicatorDiv">
              <span id="muteIndicator"></span>
          </div>
      </div>

      <div style="height:1px; background-color:#4CAF50; margin:5px 0;"></div>

      <div style="display:flex; justify-content:center; gap:13px; font-size:1.0rem; color:#999;">
          <div><span id="bankValue">Bank: --</span></div>
            <div style="display:flex; gap:6px; font-size:0.55rem; color:#999;margin:4px 0;">
              <div><span id="samplerate">---.-kHz</span></div>
              <div><span id="bitrate">---kbps</span></div>
              <div><span id="bitpersample">---bit</span></div>
              <div><span id="streamformat">----</span></div>
              WiFi: <div class="wifi-wrapper">
              <div class="wifiBar bar1" id="wifiBar1"></div>
              <div class="wifiBar bar2" id="wifiBar2"></div>
              <div class="wifiBar bar3" id="wifiBar3"></div>
              <div class="wifiBar bar4" id="wifiBar4"></div>
              <div class="wifiBar bar5" id="wifiBar5"></div>
              <div class="wifiBar bar6" id="wifiBar6"></div>
  	        </div>
          </div>
          <div><span id="stationNumber">Station: --</span></div>
      </div>
  </div>

  <br><br>

  <!-- URL + PLAY -->
  <p><input id="urlInput" type="text" placeholder="Put your URL here"></p>
  <p><button id="playBtn" class="button" onclick="playStream()">PLAY</button></p>

  <br>

  <!-- Volume -->
  <p>Volume: <span id="textSliderValue">--</span></p>
  <p><input type="range" onchange="updateSliderVolume()" id="volumeSlider" min="0" max="21" value="1" step="1" class="slider"></p>

  <p style='font-size: 0.8rem;'><a href="#" onclick="window.location.replace('/menu')">Go Back</a></p>

  <script>
  var websocket;

  function setWifi(level) 
  {
    for (let i = 1; i <= 6; i++) 
    {
      const bar = document.getElementById("wifiBar" + i);
      if (bar) {bar.style.backgroundColor = (i <= level) ? "#4CAF50" : "#555";}
    }
  }


  function connectWebSocket() 
  {
      websocket = new WebSocket('ws://' + window.location.hostname + '/ws');

      websocket.onopen = function() {
          console.log("WebSocket połączony");
      };

      websocket.onclose = function() {
          console.log("WebSocket zamknięty, reconnect za 3s...");
          setTimeout(connectWebSocket, 3000);
      };

      websocket.onerror = function(err) {
          console.error("Błąd WebSocket:", err);
          websocket.close();
      };

      websocket.onmessage = function(event) {
          const data = event.data;

          if (data.startsWith("volume:")) {
              const vol = parseInt(data.split(":")[1]);
              document.getElementById("volumeSlider").value = vol;
              document.getElementById("textSliderValue").innerText = vol;
          }

          if (data.startsWith("stationname:")) {
              const value = data.split(":")[1];
              document.getElementById("textStationName").innerHTML = "<b>" + value + "</b>";
          }

          if (data.startsWith("stationtext$")) {
              const text = data.substring(data.indexOf("$") + 1);
              document.getElementById("stationText").textContent = text;
          }

          if (data.startsWith("station:")) {
              const station = parseInt(data.split(":")[1]);
              document.getElementById("stationNumber").innerText = "Station: " + station;
          }

          if (data.startsWith("bank:")) {
              const bank = parseInt(data.split(":")[1]);
              document.getElementById("bankValue").innerText = "Bank: " + bank;
          }

          if (data.startsWith("samplerate:")) {
              const rate = parseInt(data.split(":")[1]);
              document.getElementById("samplerate").innerText = (rate / 1000).toFixed(1) + "kHz";
          }

          if (data.startsWith("bitrate:")) {
              document.getElementById("bitrate").innerText = data.split(":")[1] + "kbps";
          }

          if (data.startsWith("bitpersample:")) {
              document.getElementById("bitpersample").innerText = data.split(":")[1] + "bit";
          }

          if (data.startsWith("streamformat:")) {
              document.getElementById("streamformat").innerText = data.split(":")[1];
          }

          if (data.startsWith("mute:")) {
              const mute = parseInt(data.split(":")[1]);
              document.getElementById("muteIndicator").innerText = mute === 1 ? "MUTED" : "";
          }

          if (event.data.startsWith("wifi:")) {
            const level = parseInt(event.data.split(":")[1]);
            if (!isNaN(level)) {setWifi(Math.min(Math.max(level, 1), 6));}
          }
      };
  }

  function updateSliderVolume() {
      const slider = document.getElementById("volumeSlider");
      const value = slider.value;
      document.getElementById("textSliderValue").innerText = value;

      if (websocket && websocket.readyState === WebSocket.OPEN) {
          websocket.send("volume:" + value);
      }
  }

  function playStream() {
      const urlInput = document.getElementById("urlInput");
      const url = urlInput.value.trim();
      const host = window.location.hostname;

      urlInput.classList.add("flash");
      setTimeout(() => urlInput.classList.remove("flash"), 300);

      if (!url) return;

      fetch("http://" + host + "/update?url=" + encodeURIComponent(url))
          .catch(err => console.error("Błąd połączenia:", err));
  }

  function flashBackground() {
      const div = document.getElementById("display");
      const text = document.getElementById("textStationName");
      const origColor = div.style.backgroundColor;
      const origText = text.innerHTML;

      div.style.backgroundColor = "#115522";
      text.innerHTML = "<b>Display Mode Changed</b>";

      setTimeout(() => {
          div.style.backgroundColor = origColor;
          text.innerHTML = origText;
      }, 150);
  }

  function displayMode() {
      if (websocket && websocket.readyState === WebSocket.OPEN) {
          websocket.send("displayMode");
      }
  }

  document.addEventListener("DOMContentLoaded", () => {
      connectWebSocket();
  });
  </script>
  </body>
  </html>
)rawliteral";

const char timezone_html[] PROGMEM = R"rawliteral(
  <!DOCTYPE html>
  <html>
  <head>
  <meta charset="UTF-8">
  <title>Timezone Settings</title>
  <style>
  body { font-family: Arial; background: #D0D0D0; text-align: center; padding: 20px; }
  .tzField { width: 380px; padding: 8px; border-radius: 6px; border: 2px solid #4CAF50; font-size: 1rem; margin-bottom: 10px; text-align: left; }
  input#tzCustom { width: 380px; display: block; margin: 10px auto; text-align: center; }
  button { padding: 10px 20px; background: #4CAF50; color: white; border: 1; border-radius: 6px; cursor: pointer; font-size: 1rem; }
  button:hover { background: #3e8e41;}
  #msg { margin-top: 15px; font-weight: bold; }
  </style>
  </head>
  <body>

  <h2>Evo Web Radio - Timezone Set</h2>
  <p>Current timezone:
  <b id="currentTZ">Loading...</b></p>

  <p>Select timezone from list</p>

  <select id="tzSelect" class="tzField" onchange="selectChanged()">
      <option value="custom">Custom...</option>

      <!-- Europe -->
      <optgroup label="Europe">
          <option value="UTC0">UTC / GMT - UTC0</option>
          <option value="GMT0BST,M3.5.0/1,M10.5.0/2">United Kingdom - GMT0BST,M3.5.0/1,M10.5.0/2</option>
          <option value="CET-1CEST,M3.5.0/2,M10.5.0/3">Central Europe - CET-1CEST,M3.5.0/2,M10.5.0/3</option>
          <option value="EET-2EEST,M3.5.0/3,M10.5.0/4">Eastern Europe - EET-2EEST,M3.5.0/3,M10.5.0/4</option>
          <option value="GMT-1">Azores - GMT-1</option>
          <option value="WET0WEST,M3.5.0/1,M10.5.0/2">Portugal - WET0WEST,M3.5.0/1,M10.5.0/2</option>
          <option value="MSK-3">Moscow - MSK-3</option>
      </optgroup>

      <!-- North America -->
      <optgroup label="North America">
          <option value="EST5EDT,M3.2.0/2,M11.1.0/2">US Eastern - EST5EDT,M3.2.0/2,M11.1.0/2</option>
          <option value="CST6CDT,M3.2.0/2,M11.1.0/2">US Central - CST6CDT,M3.2.0/2,M11.1.0/2</option>
          <option value="MST7MDT,M3.2.0/2,M11.1.0/2">US Mountain - MST7MDT,M3.2.0/2,M11.1.0/2</option>
          <option value="PST8PDT,M3.2.0/2,M11.1.0/2">US Pacific - PST8PDT,M3.2.0/2,M11.1.0/2</option>
          <option value="AKST9AKDT,M3.2.0/2,M11.1.0/2">Alaska - AKST9AKDT,M3.2.0/2,M11.1.0/2</option>
          <option value="HST10">Hawaii - HST10</option>
      </optgroup>

      <!-- South America -->
      <optgroup label="South America">
          <option value="ART-3">Argentina - ART-3</option>
          <option value="BRT-3">Brazil - BRT-3</option>
          <option value="CLT-4CLST,M9.1.0/0,M4.1.0/0">Chile - CLT-4CLST,M9.1.0/0,M4.1.0/0</option>
      </optgroup>

      <!-- Asia -->
      <optgroup label="Asia">
          <option value="IST-5.5">India - IST-5.5</option>
          <option value="CST-8">China - CST-8</option>
          <option value="JST-9">Japan - JST-9</option>
          <option value="KST-9">Korea - KST-9</option>
          <option value="SGT-8">Singapore - SGT-8</option>
          <option value="WIB-7">Indonesia (WIB) - WIB-7</option>
          <option value="ICT-7">Thailand - ICT-7</option>
      </optgroup>

      <!-- Australia / Oceania -->
      <optgroup label="Australia">
          <option value="AEST-10AEDT,M10.1.0/2,M4.1.0/3">Australia Eastern - AEST-10AEDT,M10.1.0/2,M4.1.0/3</option>
          <option value="ACST-9.5ACDT,M10.1.0/2,M4.1.0/3">Australia Central - ACST-9.5ACDT,M10.1.0/2,M4.1.0/3</option>
          <option value="AWST-8">Australia Western - AWST-8</option>
      </optgroup>

      <!-- Africa -->
      <optgroup label="Africa">
          <option value="CAT-2">Central Africa - CAT-2</option>
          <option value="EAT-3">East Africa - EAT-3</option>
          <option value="WAT-1">West Africa - WAT-1</option>
          <option value="SAST-2">South Africa - SAST-2</option>
      </optgroup>
  </select>

  <input id="tzCustom" class="tzField" type="text" placeholder="Enter custom Timezone string..." readonly>

  <p id="msg"></p>
  <br>
  <button onclick="saveTZ()">Save</button>

  <p style="font-size: 0.8rem;"><a href="/menu">Go Back</a></p>

  <script>
  function loadTZ() {
      fetch("/getTZ").then(r => r.text()).then(tz => {
          document.getElementById("currentTZ").textContent = tz;
          let select = document.getElementById("tzSelect");
          let input = document.getElementById("tzCustom");
          let found = false;

          for (let i = 0; i < select.options.length; i++) {
              if (select.options[i].value === tz) {
                  select.selectedIndex = i;
                  input.value = tz;
                  input.readOnly = true;
                  input.style.display = "block";
                  found = true;
                  break;
              }
          }

          if (!found) {
              select.value = "custom";
              input.value = tz;
              input.readOnly = false;
              input.style.display = "block";
          }
      });
  }

  function selectChanged() {
      let select = document.getElementById("tzSelect");
      let input = document.getElementById("tzCustom");

      if (select.value === "custom") {
          input.readOnly = false;
          input.value = "";
          input.style.display = "block";
      } else {
          input.value = select.value;
          input.readOnly = true;
          input.style.display = "block";
      }
  }

  function saveTZ() {
      let input = document.getElementById("tzCustom");
      let tzToSave = input.value.trim();

      if (!tzToSave) {
          document.getElementById("msg").style.color = "red";
          document.getElementById("msg").textContent = "Please enter a timezone!";
          return;
      }

      fetch("/setTZ?value=" + encodeURIComponent(tzToSave))
          .then(r => r.text())
          .then(() => {
              document.getElementById("msg").style.color = "green";
              document.getElementById("msg").textContent = "Timezone saved and set.";
              loadTZ();
          })
          .catch(err => {
              document.getElementById("msg").style.color = "red";
              document.getElementById("msg").textContent = "Error: " + err;
          });
  }
  loadTZ();
  </script>
  </body>
  </html>
)rawliteral";

const char ota_html[] PROGMEM = R"rawliteral(
  <!DOCTYPE html>
  <html lang='en'>
  <head>
  <meta charset='UTF-8' />
  <meta name='viewport' content='width=device-width, initial-scale=1.0'/>
  <title>ESP OTA Update</title>
  <style>
  body { font-family: 'Segoe UI', Tahoma, Geneva, Verdana, sans-serif; background-color: #f3f4f6; color: #333; padding: 40px; text-align: center; }
  h2 { margin-bottom: 30px; color: #111; font-size: 1.3rem;}
  #uploadSection { background-color: white; padding: 30px; border-radius: 8px; display: inline-block; box-shadow: 0 0 10px rgba(0, 0, 0, 0.1); }
  input[type='file'] { padding: 10px; }
  button { margin-top: 20px; padding: 10px 20px; background-color: #4CAF50; border: none; color: white; font-size: 16px; border-radius: 5px; cursor: pointer; }
  button:disabled { background-color: #ccc; cursor: not-allowed; }
  progress { width: 100%; height: 20px; margin-top: 20px; border-radius: 5px; appearance: none; -webkit-appearance: none; }
  progress::-webkit-progress-bar { background-color: #eee; border-radius: 5px; }
  progress::-webkit-progress-value { background-color: #4CAF50; border-radius: 5px; }
  progress::-moz-progress-bar { background-color: #4CAF50; border-radius: 5px; }
  #status { margin-top: 15px; font-weight: bold; }
  #fileInfo { color: #555; margin-top: 10px; }
  </style>
  </head>
  <body>
  <div id='uploadSection'>
  <h2>Evo Web Radio - OTA Firmware Update</h2>
  <input type='file' id='fileInput' name='update' /><br />
  <div id='fileInfo'>No file selected</div>
  <button id='uploadBtn'>Upload</button>
  <p id='status'></p>
  </div>

  <script>
  const fileInput = document.getElementById('fileInput');
  const uploadBtn = document.getElementById('uploadBtn');
  const status = document.getElementById('status');
  const fileInfo = document.getElementById('fileInfo');

  fileInput.addEventListener('change', function () {
    const file = this.files[0];
    if (file) {
      fileInfo.textContent = `Selected: ${file.name} (${(file.size / 1024).toFixed(2)} KB)`;
    } else {
      fileInfo.textContent = 'No file selected';
    }
  });

  uploadBtn.addEventListener('click', function () {
    const file = fileInput.files[0];
    if (!file) { alert('Please select a file first.'); return; }
    uploadBtn.disabled = true;
    status.textContent = 'Uploading...';

    const xhr = new XMLHttpRequest();
    const formData = new FormData();
    formData.append('update', file);

    xhr.open('POST', '/firmwareota', true);

    xhr.onload = function () {
      if (xhr.status === 200) {
        status.textContent = '✅ Upload completed, reboot in 3 sec.';
        setTimeout(() => { window.location.href = '/'; }, 10000);
      } else {
        status.textContent = '❌ Upload failed.';
      }
      uploadBtn.disabled = false;
    };

    xhr.onerror = function () {
      status.textContent = '❌ Network error.';
      uploadBtn.disabled = false;
    };

    xhr.send(formData);
  });
  </script>

  </body>
  </html>
)rawliteral";


// ------------------- KONIEC STRON HTML zaszytych w kodzie -------------------

char stations[MAX_STATIONS][STATION_NAME_LENGTH + 1];  // Tablica przechowująca linki do stacji radiowych (jedna na stację) +1 dla terminatora null

const char *ntpServer1 = "pool.ntp.org";  // Adres serwera NTP używany do synchronizacji czasu
const char *ntpServer2 = "time.nist.gov"; // Adres serwera NTP używany do synchronizacji czasu
//const long gmtOffset_sec = 3600;          // Przesunięcie czasu UTC w sekundach
//const int daylightOffset_sec = 3600;      // Przesunięcie czasu letniego w sekundach, dla Polski to 1 godzina

const int LOGO_SIZE = (SCREEN_WIDTH * SCREEN_HEIGHT) / 8;
uint8_t logo_bits[LOGO_SIZE];

//Czcionka SPLEEN z polskimi znakami do obslugi radio stream tittle
const uint8_t spleen6x12PL[2958] U8G2_FONT_SECTION("spleen6x12PL") =
  "\340\1\3\2\3\4\1\3\4\6\14\0\375\10\376\11\377\1\225\3]\13q \7\346\361\363\237\0!\12"
  "\346\361#i\357`\316\0\42\14\346\361\3I\226dI\316/\0#\21\346\361\303I\64HI\226dI"
  "\64HIN\6$\22\346q\205CRK\302\61\311\222,I\206\60\247\0%\15\346\361cQK\32\246"
  "I\324\316\2&\17\346\361#Z\324f\213\22-Zr\42\0'\11\346\361#i\235\237\0(\13\346\361"
  "ia\332s\254\303\0)\12\346\361\310\325\36\63\235\2*\15\346\361S\243L\32&-\312\31\1+\13"
  "\346\361\223\323l\320\322\234\31,\12\346\361\363)\15s\22\0-\11\346\361s\32t\236\0.\10\346\361"
  "\363K\316\0/\15\346q\246a\32\246a\32\246\71\15\60\21\346\361\3S\226DJ\213\224dI\26\355"
  "d\0\61\12\346\361#\241\332\343N\6\62\16\346\361\3S\226\226\246\64\35t*\0\63\16\346\361\3S"
  "\226fr\232d\321N\6\64\14\346q\247\245\236\6\61\315\311\0\65\16\346q\17J\232\16qZ\31r"
  "\62\0\66\20\346\361\3S\232\16Q\226dI\26\355d\0\67\13\346q\17J\226\206\325v\6\70\20\346"
  "\361\3S\226d\321\224%Y\222E;\31\71\17\346\361\3S\226dI\26\15ii'\3:\11\346\361"
  "\263\346L\71\3;\13\346\361\263\346\264\64\314I\0<\12\346\361cak\334N\5=\13\346\361\263\15"
  ":\60\350\334\0>\12\346\361\3qk\330\316\2\77\14\346\361\3S\226\206\325\34\314\31@\21\346\361\3"
  "S\226dI\262$K\262\304CN\5A\22\346\361\3S\226dI\226\14J\226dI\226S\1B\22"
  "\346q\17Q\226d\311\20eI\226d\311\220\223\1C\14\346\361\3C\222\366<\344T\0D\22\346q"
  "\17Q\226dI\226dI\226d\311\220\223\1E\16\346\361\3C\222\246C\224\226\207\234\12F\15\346\361"
  "\3C\222\246C\224\266\63\1G\21\346\361\3C\222V\226,\311\222,\32r*\0H\22\346qgI"
  "\226d\311\240dI\226dI\226S\1I\12\346\361\3c\332\343N\6J\12\346\361\3c\332\233\316\2"
  "K\21\346qgI\226D\321\26\325\222,\311r*\0L\12\346q\247}\36r*\0M\20\346qg"
  "\211eP\272%Y\222%YN\5N\20\346qg\211\224HI\77)\221\222\345T\0O\21\346\361\3"
  "S\226dI\226dI\226d\321N\6P\17\346q\17Q\226dI\226\14QZg\2Q\22\346\361\3"
  "S\226dI\226dI\226d\321\252\303\0R\22\346q\17Q\226dI\226\14Q\226dI\226S\1S"
  "\16\346\361\3C\222\306sZ\31r\62\0T\11\346q\17Z\332w\6U\22\346qgI\226dI\226"
  "dI\226d\321\220S\1V\20\346qgI\226dI\226dI\26m;\31W\21\346qgI\226d"
  "I\226\264\14\212%\313\251\0X\21\346qgI\26%a%\312\222,\311r*\0Y\20\346qgI"
  "\226dI\26\15ie\310\311\0Z\14\346q\17j\330\65\35t*\0[\13\346\361\14Q\332\257C\16"
  "\3\134\15\346q\244q\32\247q\32\247\71\14]\12\346\361\14i\177\32r\30^\12\346\361#a\22e"
  "\71\77_\11\346\361\363\353\240\303\0`\11\346\361\3q\235_\0a\16\346\361S\347hH\262$\213\206"
  "\234\12b\20\346q\247\351\20eI\226dI\226\14\71\31c\14\346\361S\207$m\36r*\0d\21"
  "\346\361ci\64$Y\222%Y\222ECN\5e\17\346\361S\207$K\262dP\342!\247\2f\14"
  "\346\361#S\32\16Y\332\316\2g\21\346\361S\207$K\262$K\262hN\206\34\1h\20\346q\247"
  "\351\20eI\226dI\226d\71\25i\13\346\361#\71\246v\325\311\0j\13\346\361C\71\230\366\246S"
  "\0k\16\346q\247\245J&&YT\313\251\0l\12\346\361\3i\237u\62\0m\15\346\361\23\207("
  "\351\337\222,\247\2n\20\346\361\23\207(K\262$K\262$\313\251\0o\16\346\361S\247,\311\222,"
  "\311\242\235\14p\21\346\361\23\207(K\262$K\262d\210\322*\0q\20\346\361S\207$K\262$K"
  "\262hH[\0r\14\346\361S\207$K\322v&\0s\15\346\361S\207$\236\323d\310\311\0t\13"
  "\346\361\3i\70\246\315:\31u\20\346\361\23\263$K\262$K\262h\310\251\0v\16\346\361\23\263$"
  "K\262$\213\222\60gw\17\346\361\23\263$KZ\6\305\222\345T\0x\16\346\361\23\263$\213\266)"
  "K\262\234\12y\22\346\361\23\263$K\262$K\262hH\223!G\0z\14\346\361\23\7\65l\34t"
  "*\0{\14\346\361iiM\224\323\262\16\3|\10\346q\245\375;\5}\14\346\361\310iY\324\322\232"
  "N\1~\12\346\361s\213\222D\347\10\177\7\346\361\363\237\0\200\6\341\311\243\0\201\6\341\311\243\0\202"
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
  "\6t\10t\334\320(&\5u\12u}X(\22\212\220\1v\12u}X(\22\12\311\1w\11v"
  "~h$/u\0x\11t|HRJ\24\0y\13u}X(\22\212\20#\0z\10u}\30-"
  "D\6{\10t\34QbL\12|\7r\212Hn\0}\11t\14Y\60\24\22\3~\7u\235\334\261"
  "\0\177\7t\14\221\316\0\0\0\0\4\377\377\0"
;

// Ikona karty SD wyswietlana przy braku karty podczas startu
static unsigned char sdcard[] PROGMEM = {
  0xf0, 0xff, 0xff, 0x0f, 0xf8, 0xff, 0xff, 0x1f, 0xf8, 0xcf, 0xf3, 0x3f,
  0x38, 0x49, 0x92, 0x3c, 0x38, 0x49, 0x92, 0x3c, 0x38, 0x49, 0x92, 0x3c,
  0x38, 0x49, 0x92, 0x3c, 0x38, 0x49, 0x92, 0x3c, 0x38, 0x49, 0x92, 0x3c,
  0x38, 0x49, 0x92, 0x3c, 0xf8, 0xff, 0xff, 0x3f, 0xf8, 0xff, 0xff, 0x3f,
  0xf8, 0xff, 0xff, 0x3f, 0xf8, 0xff, 0xff, 0x3f, 0xf8, 0xff, 0xff, 0x3f,
  0xfc, 0xff, 0xff, 0x3f, 0xfe, 0xff, 0xff, 0x3f, 0xff, 0xff, 0xff, 0x3f,
  0xff, 0xff, 0xff, 0x3f, 0xff, 0xff, 0xff, 0x3f, 0xff, 0xff, 0xff, 0x3f,
  0xfc, 0xff, 0xff, 0x3f, 0xfc, 0xc0, 0x80, 0x3f, 0x7c, 0xc0, 0x00, 0x3f,
  0x3c, 0xc0, 0x00, 0x3e, 0x1c, 0xfc, 0x38, 0x3e, 0x1e, 0xfc, 0x78, 0x3c,
  0x1f, 0xe0, 0x78, 0x3c, 0x3f, 0xc0, 0x78, 0x3c, 0x7f, 0x80, 0x78, 0x3c,
  0xff, 0x87, 0x78, 0x3c, 0xff, 0x87, 0x38, 0x3e, 0x3f, 0x80, 0x00, 0x3e,
  0x1f, 0xc0, 0x00, 0x3f, 0x3f, 0xe0, 0x80, 0x3f, 0xff, 0xff, 0xff, 0x3f,
  0xff, 0xff, 0xff, 0x3f, 0xff, 0xff, 0xff, 0x3f, 0xfe, 0xff, 0xff, 0x1f,
  0xfc, 0xff, 0xff, 0x0f 
};
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
void loop() 
{
  runTime1 = esp_timer_get_time();
  audio.loop();           // Wykonuje główną pętlę dla obiektu audio
  button2.loop();         // Wykonuje pętlę dla obiektu button2 (sprawdza stan przycisku z enkodera 2)
  handleButtons();        // Wywołuje dodatkowe funkcję obsługującą przyciski enkoderow
  handleFadeIn();         // Obsługa sciszania stacji przy przełaczaniu
  vTaskDelay(2);          // Krótkie opóźnienie, oddaje czas procesora innym zadaniom
  
  #ifdef SERIALCOM
    handleSerialRX();
  #endif
    
  /*---------------------  FUNKCJA PILOT IR  / Obsluga pilota IR w kodzie NEC ---------------------*/ 
  handleRemoteIR();         

  /*-- FUNKCJA KLAWIATURA / Odczyt stanu klawiatura ADC ---------------------*/ 
  if ((millis() - keyboardLastSampleTime >= keyboardSampleDelay) && adcKeyboardEnabled) // Sprawdzenie ADC - klawiatury 
  {
    handleAdcKeyboard();
    keyboardLastSampleTime = millis();
  }
  


  /*-- ENKODER 1 - obsluga opcjonlanego enkodera 1 ---------------------*/
  #ifdef twoEncoders
    button1.loop();
    handleEncoder1();
  #endif

  /*-- ENKODER 2 - Podstaowy, obsluga enkodera 2 ---------------------*/
  if (encoderFunctionOrder) { handleEncoder2StationsVolumeClick();} else {handleEncoder2VolumeStationsClick();}

  
  // Obsługa przycisku Power ON/OFF
  #ifdef SW_POWER
    if (digitalRead(SW_POWER) == LOW) {powerOff();}
  #endif

  /*---------------------  FUNKCJA DIMMER ---------------------*/
  if (displayActive && displayDimmerActive && !fwupd) {displayDimmer(0);}  

  
  /*---------------------  FUNKCJA BACK / POWROTU ze wszystkich opcji Menu, Ustawien, itd ---------------------*/
  if (!fwupd && displayActive && (millis() - displayStartTime >= displayTimeout)) // Przywracanie poprzedniej zawartości ekranu po czasie timeout
  {
    backToMainScreen();
  }


  /*---------------------  FUNKCJA PETLI MILLIS SCROLLER / Odswiezanie VU Meter, Time, Scroller, OLED, WiFi ver. 1 ---------------------*/ 
  
  if ((millis() - scrollingStationStringTime > scrollingRefresh) && (!displayActive))
  {
    scrollingStationStringTime = millis();
    
    // Aktualizacja zegara, zegar głosowy, debug Audio, sygnał wifi 
    if (ActionNeedUpdateTime == true) 
    {
      ActionNeedUpdateTime = false;
      updateTime();
      
      // Zegar głosowy, sprawdzamy czy została ustawiona flaga zegara przy pełnej godzinie
      if (f_requestVoiceTimePlay == true) {f_requestVoiceTimePlay = false; voiceTime();}

      if (debugAudioBuffor == true) {bufforAudioInfo();}
      
      if ((displayMode == 0) || (displayMode == 2))  {drawSignalPower(210,63,0,1);}
      if ((displayMode == 1) && (volumeMute == false)) {drawSignalPower(244,47,0,1);}
      if (displayMode == 3) {drawSignalPower(209,10,0,1);}


      if (wifiSignalLevel != wifiSignalLevelLast) {wifiSignalLevelLast = wifiSignalLevel; wsSignalLevel();}


      if ((f_audioInfoRefreshStationString == true) && (displayActive == false)) // Zmiana streamtitle - wymaga odswiezenia na wyswietlaczu
      { 
        f_audioInfoRefreshStationString = false; //NewAudioInfoSSF
        stationStringFormatting(); // Formatujemy StationString do wyswietlenia przez Scroller
      } 

      if ((f_audioInfoRefreshDisplayRadio == true) && (displayActive == false)) //&& (f_requestVoiceTimePlay == false) Zmiana bitrate - wymaga odswiezenia na wyswietlaczu
      { 
        f_audioInfoRefreshDisplayRadio = false;
        ActionNeedUpdateTime = true;
        displayRadio();
      } 
      
      if (wsAudioRefresh == true) // Web Socket StremInfo wymaga odswiezenia
      {
        wsAudioRefresh = false;
        wsStreamInfoRefresh();
      }
      
    }

    if (volumeMute == false) // Jezeli mute OFF to rysujemy VU
    {
      if (vuMeterOn)
      { 
        if (displayMode == 0) {vuMeterMode0();}
        if (displayMode == 3) {vuMeterMode3();}
        if (displayMode == 4) 
        {
          vuMeterMode4(); 
          if (debugAudioBuffor) // Wskaznik bufora audio w trybie wskaznikow analogowych
          {
            for (int i = 0; i < 10; i++) 
            {
              int y = 1 + (9 - i) * 6; 
              if (audioBufferTime > i) { u8g2.drawBox(126, y, 8, 5);} else {u8g2.drawFrame(126, y, 8, 5);}
            }
          }
        }
        if (displayMode == 5) {vuMeterMode5();}
        if (displayMode == 7) {vuMeterMode7();}
      }
      else if (displayMode == 0) {showIP(1,47);} //y = vuRy
    }
    else // Jesli MUTE to zamiast VU wprowadzamy napis MUTE na ekran
    {
      u8g2.setDrawColor(0);
      if (displayMode == 0) {u8g2.drawStr(0,48, "> MUTED <");}
      if (displayMode == 1) {u8g2.drawStr(200,47, "> MUTED <");}
      if (displayMode == 2) {u8g2.drawStr(0,48, "> MUTED <");}
      if (displayMode == 3) {u8g2.drawStr(101,63, "> MUTED <");}
      if (displayMode == 4) {u8g2.setDrawColor(1); vuMeterMode4(); u8g2.setDrawColor(1); u8g2.setFont(spleen6x12PL); u8g2.setDrawColor(0); u8g2.drawStr(103,57, "> MUTED <");}
      u8g2.setDrawColor(1);
    }  
       
    if (urlToPlay == true) // Jesli web serwer ustawił flagę "odtwarzaj URL" to uruchamiamy funkcje odtwarzania z adresu URL wysłanego przez strone WWW
    {
      urlToPlay = false;
      webUrlStationPlay();
      displayRadio();
    }
    
    displayRadioScroller();  // wykonujemy przewijanie tekstu station stringi przygotowujemy bufor ekranu
    u8g2.sendBuffer();  // rysujemy całą zawartosc ekranu.
    
    //if (f_callInfo) {f_callInfo = false; displayInfo();}  
    
  }
  //runTime2 = esp_timer_get_time();
  //runTime = runTime2 - runTime1;
}
